QuickMick/zeta2/pcb/smd/zeta2/zeta2rework_lw_v6.brd

## EAGLE design pcb/smd/zeta2/zeta2rework_lw_v6.brd (2019-02-10, an earlier design)

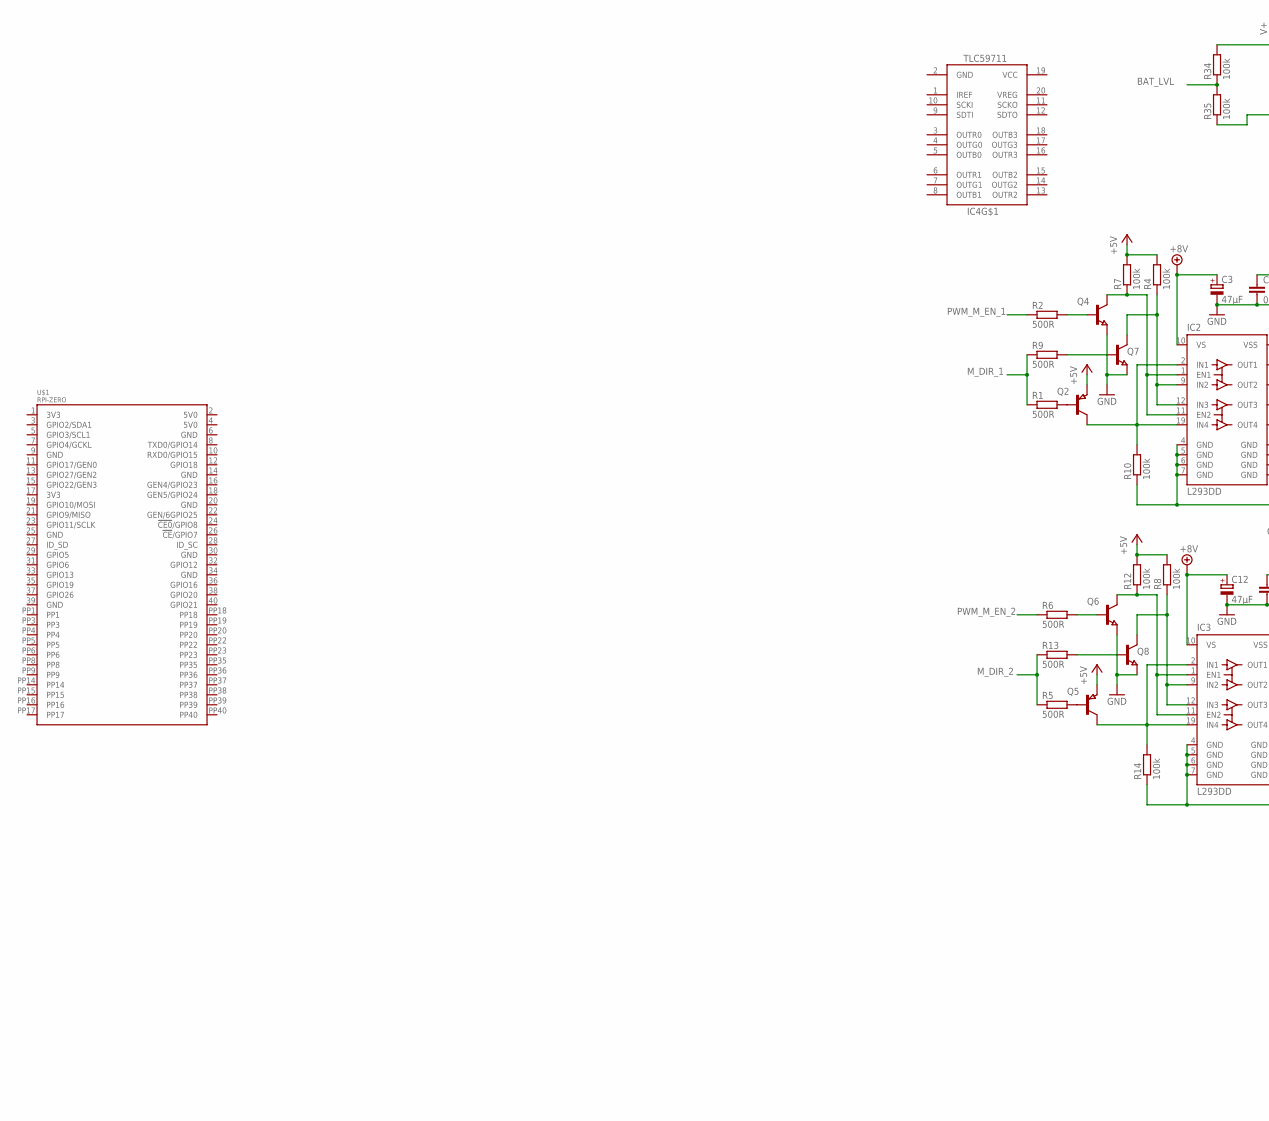
[picture p16: schematic zeta2rework_lw_v6.sch, part in row 1, column 1]

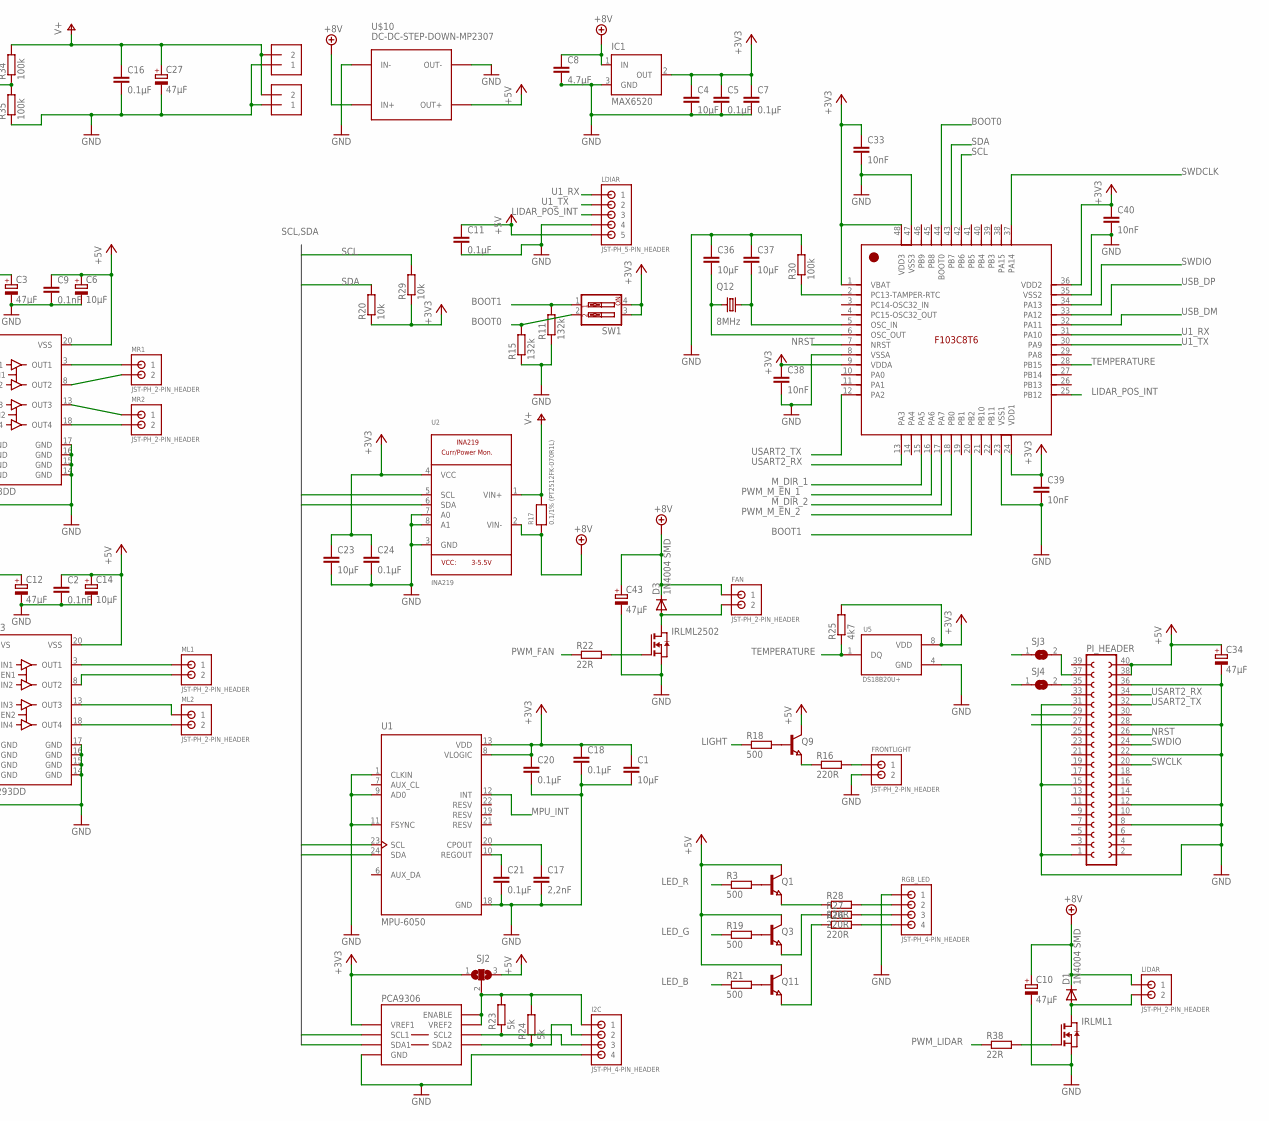
[picture p17: schematic zeta2rework_lw_v6.sch, part in row 1, column 2]

Parts:
C1, C4, C23, C36, C37: 10µF; C1206
C2, C9: 0.1nF; C1206
C3, C10, C12, C27, C34, C43: 47µF; UD-4X5,8_NICHICON
C5, C7, C11, C16, C18, C20, C21, C24: 0.1µF; C1206
C6, C14: 10µF; UD-4X5,8_NICHICON
C8: 4.7µF; C1206
C17: 2,2nF; C1206
C33, C38, C39, C40: 10nF; C1206
D1, D3: 1N4004 SMD; DO214AC
FAN: JST-PH_2-PIN_HEADER; JST_B2B-PH_HEADER
FRONTLIGHT: JST-PH_2-PIN_HEADER; JST_B2B-PH_HEADER
I2C: JST-PH_4-PIN_HEADER; JST_B4B-PH_HEADER
IC1: MAX6520; SOT23
IC2, IC3: L293DD; SO20
IC4: TLC59711; HTSSOP20DAP
IRLML1, IRLML2502: NMOSSOT23; SOT-23
LDIAR: JST-PH_5-PIN_HEADER; JST_B5B-PH_HEADER
LIDAR: JST-PH_2-PIN_HEADER; JST_B2B-PH_HEADER
ML1, ML2: JST-PH_2-PIN_HEADER; JST_B2B-PH_HEADER
MR1, MR2: JST-PH_2-PIN_HEADER; JST_B2B-PH_HEADER
PCA9306: IC2_LEVEL_TRANSLATER; SOIC-8
PI_HEADER: FE20-2
Q1, Q3, Q4, Q6, Q7, Q8, Q9, Q11: NPN-TRANSISTOR_SOT23; SOT23
Q2, Q5: PNP-TRANSISTOR_SOT23; SOT23
Q12: 8MHz; 7.0X5.0
R1, R2, R5, R6, R9, R13: 500R; R0603
R3, R19, R21: 500; R0603
R4, R7, R8, R10, R12, R14, R30, R34, R35: 100k; R0603
R11, R15: 132k; R0603
R16, R26, R27, R28: 220R; R0603
R17: 0.1/1% (PT2512FK-070R1L); 2512
R18: 500; R1206
R20, R29: 10k; R0603
R22, R38: 22R; R0603
R23, R24: 5k; R0603
R25: 4k7; R0603
RGB_LED: JST-PH_4-PIN_HEADER; JST_B4B-PH_HEADER
SJ2: SJ2W; SJ_2
SJ3, SJ4: SOLDERJUMPERREFLOW_NOPASTE; SOLDERJUMPER_REFLOW_NOPASTE
STM32F103CB: STM32F103CB; LQFP48_7X7MM_0.5MMPP
SUPPLY_IN, SUPPLY_IN1: TERMBLOCK_1X2-3.5MM; 1X2-3.5MM
SW1: SW_DIP-2; EDG-02
U1: MPU-6050; QFN50P400X400X95-24N
U2: INA219; SOT23-8
U5: DS18B20U+; SOP65P490X95-8N
U$1: RPI-ZERO; RASP_PI_ZERO_BOARD_FULL
U$10: DC-DC-STEP-DOWN-MP2307

Connections:
+3V3: C1.1, C4.1, C5.1, C7.1, C18.1, C20.1, C23.1, C24.1, C33.1, C38.1, C39.1, C40.1, IC1.2 (OUT), PCA9306.1 (VREF1), R20.1, R25.2, R29.1, SJ2.1, STM32F103CB.1 (VBAT), STM32F103CB.9 (VDDA), STM32F103CB.24 (VDD1), STM32F103CB.36 (VDD2), STM32F103CB.48 (VDD3), SW1.3, SW1.4, U1.8 (VLOGIC), U1.13 (VDD), U2.4 (VCC), U5.8 (VDD)
+5V: C2.1, C6.+, C9.1, C11.1, C14.+, C34.+, IC2.20 (VSS), IC3.20 (VSS), LDIAR.P5 (5), PI_HEADER.38, PI_HEADER.40, Q1.3 (C), Q2.2 (E), Q3.3 (C), Q5.2 (E), Q9.3 (C), Q11.3 (C), R4.2, R7.2, R8.2, R12.2, SJ2.3, U$10.OUT+
+8V: C3.+, C8.1, C10.+, C12.+, C43.+, D1.C, D3.C, FAN.P1 (1), IC1.1 (IN), IC2.10 (VS), IC3.10 (VS), LIDAR.P1 (1), R17.1, U2.2 (VIN-), U$10.IN+
BAT_LVL: R34.1, R35.2
BOOT0: R15.2, STM32F103CB.44 (BOOT0), SW1.2
BOOT1: R11.2, STM32F103CB.20 (PB2), SW1.1
BOOT2: PI_HEADER.29
BOOT3: PI_HEADER.27
GND: C1.2, C2.2, C3.-, C4.2, C5.2, C6.-, C7.2, C8.2, C9.2, C10.-, C11.2, C12.-, C14.-, C16.2, C17.2, C18.2, C20.2, C21.2, C23.2, C24.2, C27.-, C33.2, C34.-, C36.1, C37.1, C38.2, C39.2, C40.2, C43.-, FRONTLIGHT.P2 (2), I2C.P4 (4), IC1.3 (GND), IC2.4 (GND), IC2.5 (GND), IC2.6 (GND), IC2.7 (GND), IC2.14 (GND), IC2.15 (GND), IC2.16 (GND), IC2.17 (GND), IC3.4 (GND), IC3.5 (GND), IC3.6 (GND), IC3.7 (GND), IC3.14 (GND), IC3.15 (GND), IC3.16 (GND), IC3.17 (GND), IC4.2 (GND), IRLML1.2 (S), IRLML2502.2 (S), LDIAR.P4 (4), PCA9306.4 (GND), PI_HEADER.1, PI_HEADER.8, PI_HEADER.12, PI_HEADER.15, PI_HEADER.22, PI_HEADER.28, PI_HEADER.31, PI_HEADER.36, Q4.2 (E), Q6.2 (E), Q7.2 (E), Q8.2 (E), R10.1, R11.1, R14.1, R15.1, R30.2, R35.1, RGB_LED.P1 (1), STM32F103CB.8 (VSSA), STM32F103CB.23 (VSS1), STM32F103CB.35 (VSS2), STM32F103CB.47 (VSS3), SUPPLY_IN.1, SUPPLY_IN1.1, U1.1 (CLKIN), U1.9 (AD0), U1.11 (FSYNC), U1.18 (GND), U2.3 (GND), U2.7 (A0), U2.8 (A1), U5.4 (GND), U$10.IN-, U$10.OUT-
LED_B: R21.1
LED_G: R19.1
LED_R: R3.1
LIDAR_POS_INT: LDIAR.P3 (3), STM32F103CB.25 (PB12)
LIGHT: R18.1
MPU_INT: U1.12 (INT)
M_DIR_1: R1.1, R9.1, STM32F103CB.15 (PA5)
M_DIR_2: R5.1, R13.1, STM32F103CB.17 (PA7)
unnamed: IC2.9 (IN2), IC2.12 (IN3), Q7.3 (C), R4.1
unnamed: IC3.18 (OUT4), ML2.P2 (2)
unnamed: IC3.13 (OUT3), ML2.P1 (1)
unnamed: IC2.18 (OUT4), MR2.P2 (2)
unnamed: IC2.2 (IN1), IC2.19 (IN4), Q2.3 (C), R10.2
unnamed: IC3.9 (IN2), IC3.12 (IN3), Q8.3 (C), R8.1
unnamed: IC3.2 (IN1), IC3.19 (IN4), Q5.3 (C), R14.2
unnamed: IC2.1 (EN1), IC2.11 (EN2), Q4.3 (C), R7.1
unnamed: IC3.1 (EN1), IC3.11 (EN2), Q6.3 (C), R12.1
unnamed: Q2.1 (B), R1.2
unnamed: Q4.1 (B), R2.2
unnamed: Q7.1 (B), R9.2
unnamed: Q5.1 (B), R5.2
unnamed: Q6.1 (B), R6.2
unnamed: Q8.1 (B), R13.2
unnamed: IC2.13 (OUT3), MR2.P1 (1)
unnamed: IC2.8 (OUT2), MR1.P2 (2)
unnamed: IC2.3 (OUT1), MR1.P1 (1)
unnamed: Q9.1 (B), R18.2
unnamed: Q9.2 (E), R16.1
unnamed: FRONTLIGHT.P1 (1), R16.2
unnamed: Q1.1 (B), R3.2
unnamed: Q3.1 (B), R19.2
unnamed: Q1.2 (E), R28.1
unnamed: IC3.8 (OUT2), ML1.P2 (2)
unnamed: IC3.3 (OUT1), ML1.P1 (1)
unnamed: Q3.2 (E), R27.1
unnamed: Q11.2 (E), R26.1
unnamed: R26.2, RGB_LED.P4 (4)
unnamed: Q11.1 (B), R21.2
unnamed: R27.2, RGB_LED.P3 (3)
unnamed: C17.1, U1.20 (CPOUT)
unnamed: R28.2, RGB_LED.P2 (2)
unnamed: C21.1, U1.10 (REGOUT)
unnamed: IRLML2502.3 (G), R22.2
unnamed: IRLML1.3 (G), R38.2
unnamed: D1.A, IRLML1.1 (D), LIDAR.P2 (2)
unnamed: I2C.P1 (1), PCA9306.7 (VREF2), PCA9306.8 (ENABLE), R23.2, R24.2, SJ2.2
unnamed: I2C.P3 (3), PCA9306.6 (SCL2), R23.1
unnamed: I2C.P2 (2), PCA9306.5 (SDA2), R24.1
unnamed: PI_HEADER.37, SJ3.2
unnamed: PI_HEADER.35, SJ4.2
unnamed: C36.2, Q12.1, STM32F103CB.6 (OSC_OUT)
unnamed: C37.2, Q12.3 (2), STM32F103CB.5 (OSC_IN)
unnamed: R30.1, STM32F103CB.2 (PC13-TAMPER-RTC)
unnamed: D3.A, FAN.P2 (2), IRLML2502.1 (D)
NRST: PI_HEADER.26, STM32F103CB.7 (NRST)
PWM_FAN: R22.1
PWM_LIDAR: R38.1
PWM_M_EN_1: R2.1, STM32F103CB.16 (PA6)
PWM_M_EN_2: R6.1, STM32F103CB.18 (PB0)
SCL: R29.2, STM32F103CB.42 (PB6), U1.23 (SCL), U2.5 (SCL)
SCL2: PCA9306.2 (SCL1)
SCL3: SJ4.1
SDA: R20.2, STM32F103CB.43 (PB7), U1.24 (SDA), U2.6 (SDA)
SDA2: PCA9306.3 (SDA1)
SDA3: SJ3.1
SWCLK: PI_HEADER.20
SWDCLK: STM32F103CB.37 (PA14)
SWDIO: PI_HEADER.24, STM32F103CB.34 (PA13)
TEMPERATURE: R25.1, STM32F103CB.28 (PB15), U5.1 (DQ)
U1_RX: LDIAR.P1 (1), STM32F103CB.31 (PA10)
U1_TX: LDIAR.P2 (2), STM32F103CB.30 (PA9)
USART2_RX: PI_HEADER.34, STM32F103CB.13 (PA3)
USART2_TX: PI_HEADER.32, STM32F103CB.12 (PA2)
USB_DM: STM32F103CB.32 (PA11)
USB_DP: STM32F103CB.33 (PA12)
V+: C16.1, C27.+, R17.2, R34.2, SUPPLY_IN.2, SUPPLY_IN1.2, U2.1 (VIN+)
VCC: IC4.19 (VCC)

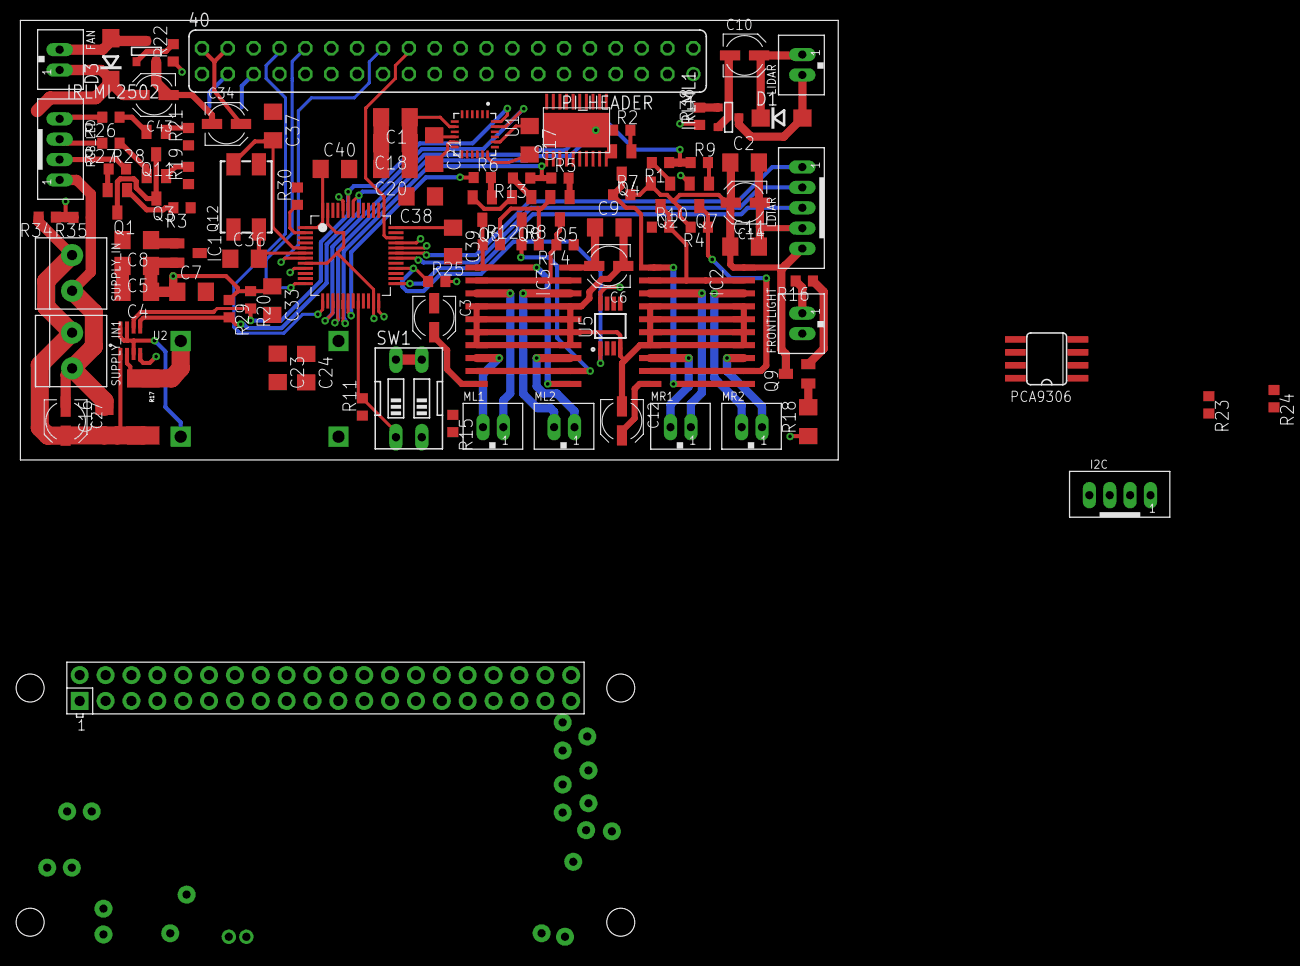
[picture p18: board zeta2rework_lw_v6.brd from above]

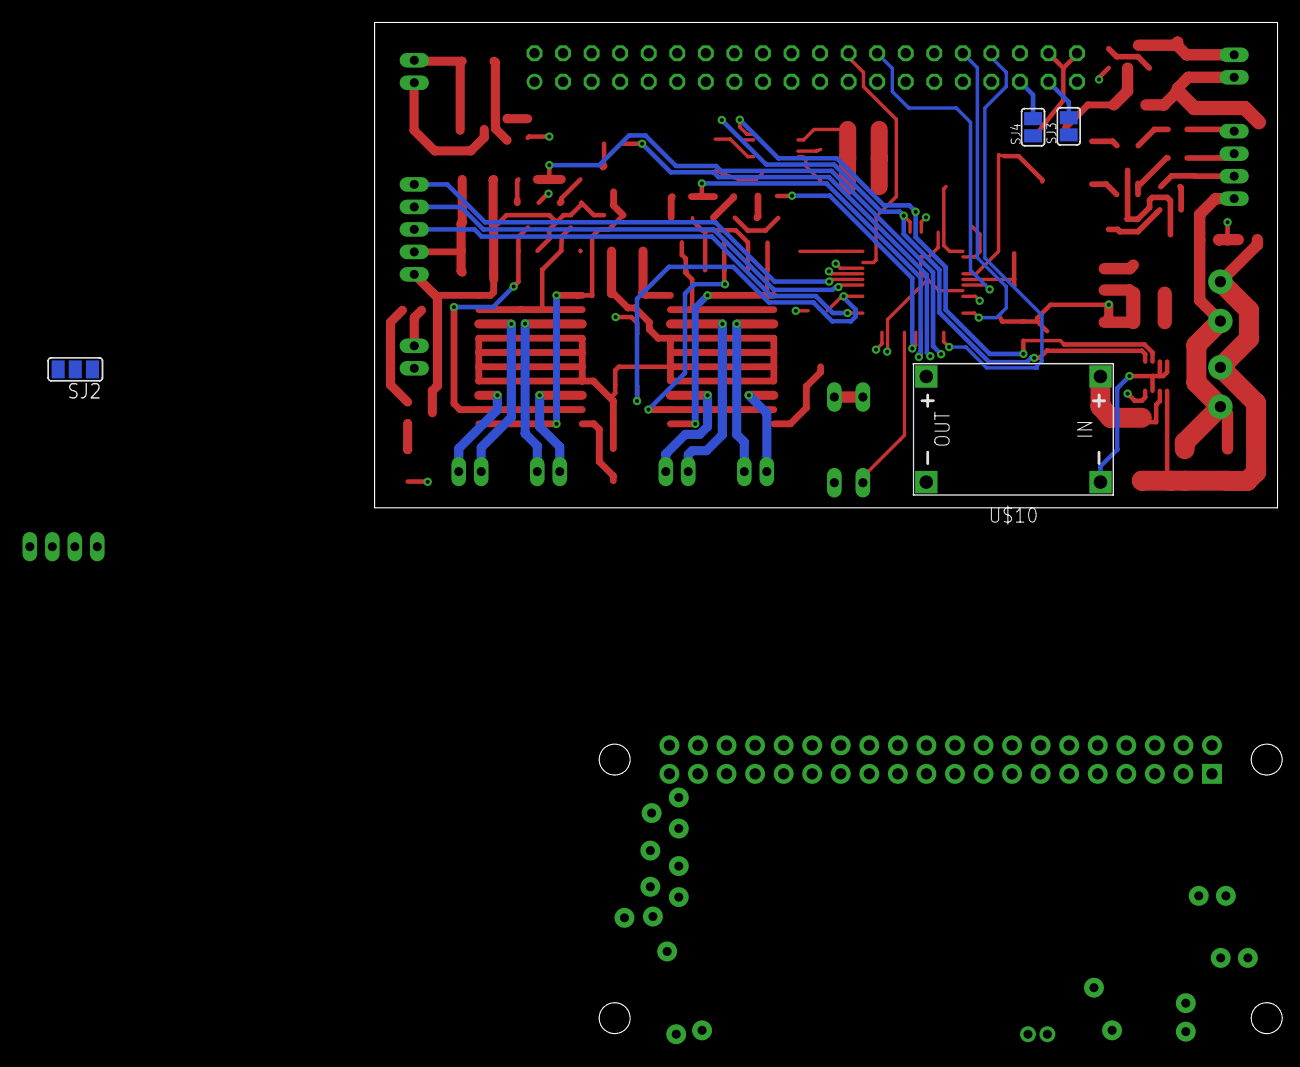
[picture p19: board zeta2rework_lw_v6.brd from below]

Board: 2 copper layers, 80.3 x 43.2 mm, 105 parts (4 on the bottom side), 68 nets.
