QuickMick/zeta2/pcb/smd/zeta2/zeta2rework_lw_v16.brd

## EAGLE design pcb/smd/zeta2/zeta2rework_lw_v16.brd (2019-02-10, an earlier design)

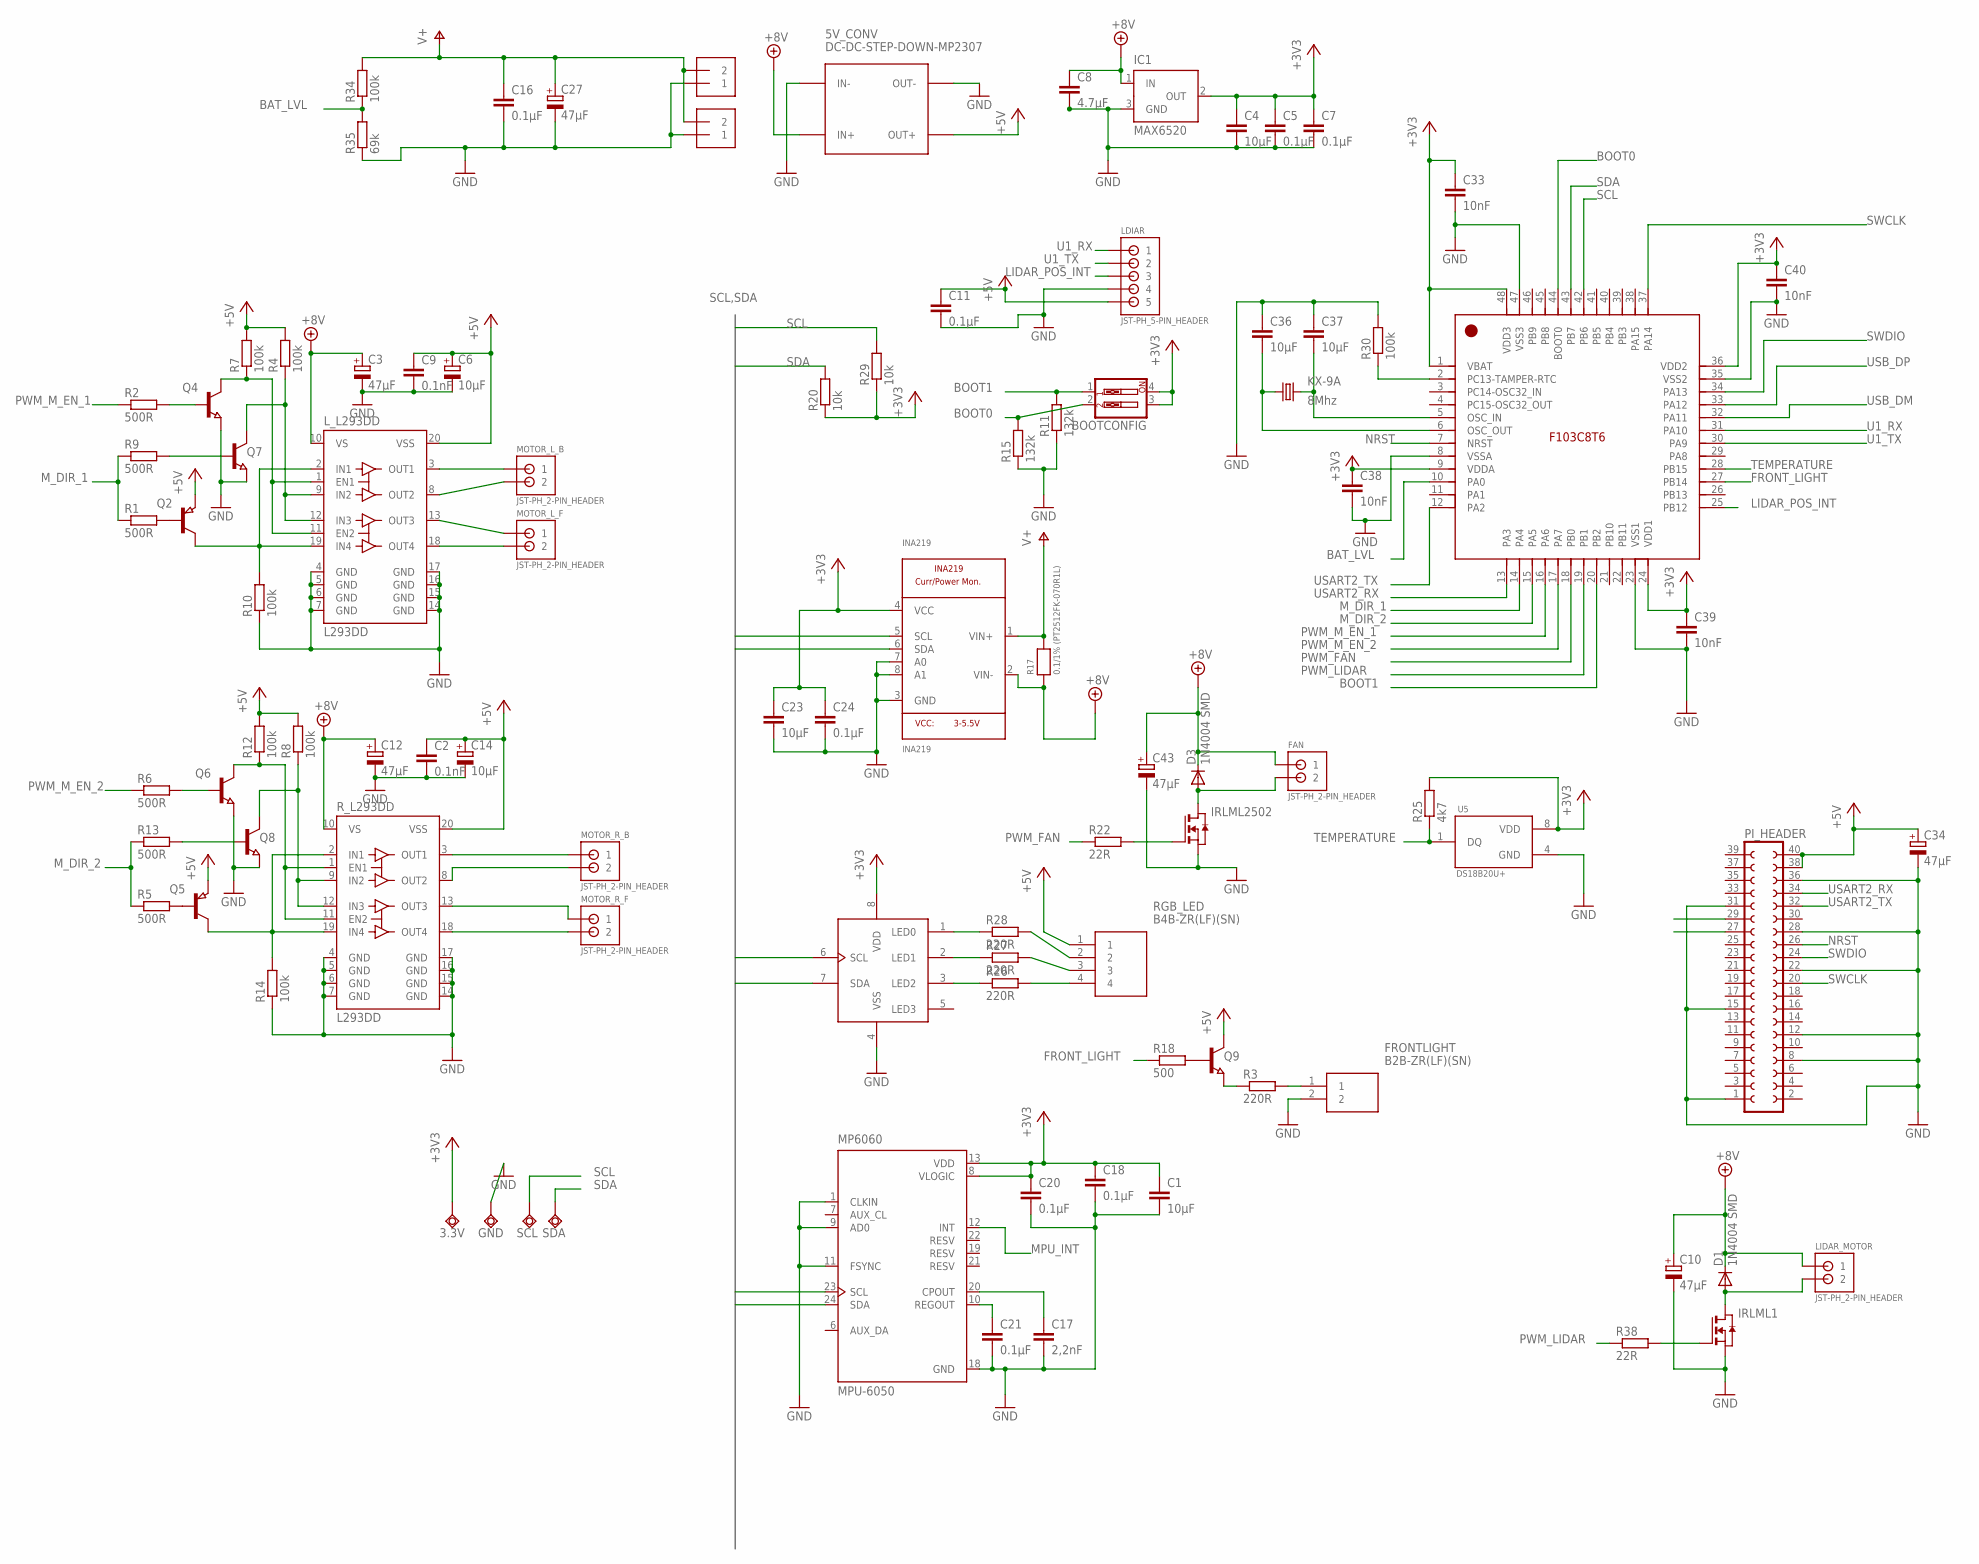
[picture p20: schematic zeta2rework_lw_v16.sch]

Parts:
3.3V: TPSQTP20R; TP20R
5V_CONV: DC-DC-STEP-DOWN-MP2307
BOOTCONFIG: SW_DIP-2; EDG-02
C1, C4, C23, C36, C37: 10µF; C1206
C2, C9: 0.1nF; C1206
C3, C10, C12, C27, C34, C43: 47µF; UD-4X5,8_NICHICON
C5, C7, C11, C16, C18, C20, C21, C24: 0.1µF; C1206
C6, C14: 10µF; UD-4X5,8_NICHICON
C8: 4.7µF; C1206
C17: 2,2nF; C1206
C33, C38, C39, C40: 10nF; C1206
D1, D3: 1N4004 SMD; DO214AC
FAN: JST-PH_2-PIN_HEADER; JST_B2B-PH_HEADER
FRONTLIGHT: B2B-ZR(LF)(SN); SHDR2W50P0X150_1X2_450X350X450
GND: TPSQTP20R; TP20R
IC1: MAX6520; SOT23
INA219: INA219; SOT23-8
IRLML1, IRLML2502: NMOSSOT23; SOT-23
KX-9A: 8Mhz; 5.0X3.2_KX-9A
LDIAR: JST-PH_5-PIN_HEADER; JST_B5B-PH_HEADER
LIDAR_MOTOR: JST-PH_2-PIN_HEADER; JST_B2B-PH_HEADER
L_L293DD: L293DD; SO20
MOTOR_L_B: JST-PH_2-PIN_HEADER; JST_B2B-PH_HEADER
MOTOR_L_F: JST-PH_2-PIN_HEADER; JST_B2B-PH_HEADER
MOTOR_R_B: JST-PH_2-PIN_HEADER; JST_B2B-PH_HEADER
MOTOR_R_F: JST-PH_2-PIN_HEADER; JST_B2B-PH_HEADER
MP6060: MPU-6050; QFN50P400X400X95-24N
PCA9533: PCA9533; SOIC8
PI_HEADER: FE20-2
Q2, Q5: PNP-TRANSISTOR_SOT23; SOT23
Q4, Q6, Q7, Q8, Q9: NPN-TRANSISTOR_SOT23; SOT23
R1, R2, R5, R6, R9, R13: 500R; R0603
R3, R26, R27, R28: 220R; R0603
R4, R7, R8, R10, R12, R14, R30, R34: 100k; R0603
R11, R15: 132k; R0603
R17: 0.1/1% (PT2512FK-070R1L); 2512
R18: 500; R1206
R20, R29: 10k; R0603
R22, R38: 22R; R0603
R25: 4k7; R0603
R35: 69k; R0603
RGB_LED: B4B-ZR(LF)(SN); SHDR4W50P0X150_1X4_750X350X450
R_L293DD: L293DD; SO20
SCL: TPSQTP20R; TP20R
SDA: TPSQTP20R; TP20R
STM32F103CB: STM32F103CB; LQFP48_7X7MM_0.5MMPP
SUPPLY_IN, SUPPLY_IN1: TERMBLOCK_1X2-3.5MM; 1X2-3.5MM
U5: DS18B20U+; SOP65P490X95-8N

Connections:
+3V3: 3.3V.TP, BOOTCONFIG.3, BOOTCONFIG.4, C1.1, C4.1, C5.1, C7.1, C18.1, C20.1, C23.1, C24.1, C33.1, C38.1, C39.1, C40.1, IC1.2 (OUT), INA219.4 (VCC), MP6060.8 (VLOGIC), MP6060.13 (VDD), PCA9533.8 (VDD), R20.1, R25.2, R29.1, STM32F103CB.1 (VBAT), STM32F103CB.9 (VDDA), STM32F103CB.24 (VDD1), STM32F103CB.36 (VDD2), STM32F103CB.48 (VDD3), U5.8 (VDD)
+5V: 5V_CONV.OUT+, C2.1, C6.+, C9.1, C11.1, C14.+, C34.+, LDIAR.P5 (5), L_L293DD.20 (VSS), PI_HEADER.38, PI_HEADER.40, Q2.2 (E), Q5.2 (E), Q9.3 (C), R4.2, R7.2, R8.2, R12.2, RGB_LED.1, R_L293DD.20 (VSS)
+8V: 5V_CONV.IN+, C3.+, C8.1, C10.+, C12.+, C43.+, D1.C, D3.C, FAN.P1 (1), IC1.1 (IN), INA219.2 (VIN-), LIDAR_MOTOR.P1 (1), L_L293DD.10 (VS), R17.1, R_L293DD.10 (VS)
BAT_LVL: R34.1, R35.2, STM32F103CB.10 (PA0)
BOOT0: BOOTCONFIG.2, R15.2, STM32F103CB.44 (BOOT0)
BOOT1: BOOTCONFIG.1, R11.2, STM32F103CB.20 (PB2)
BOOT2: PI_HEADER.29
BOOT3: PI_HEADER.27
FRONT_LIGHT: R18.1, STM32F103CB.27 (PB14)
GND: 5V_CONV.IN-, 5V_CONV.OUT-, C1.2, C2.2, C3.-, C4.2, C5.2, C6.-, C7.2, C8.2, C9.2, C10.-, C11.2, C12.-, C14.-, C16.2, C17.2, C18.2, C20.2, C21.2, C23.2, C24.2, C27.-, C33.2, C34.-, C36.1, C37.1, C38.2, C39.2, C40.2, C43.-, FRONTLIGHT.2, GND.TP, IC1.3 (GND), INA219.3 (GND), INA219.7 (A0), INA219.8 (A1), IRLML1.2 (S), IRLML2502.2 (S), LDIAR.P4 (4), L_L293DD.4 (GND), L_L293DD.5 (GND), L_L293DD.6 (GND), L_L293DD.7 (GND), L_L293DD.14 (GND), L_L293DD.15 (GND), L_L293DD.16 (GND), L_L293DD.17 (GND), MP6060.1 (CLKIN), MP6060.9 (AD0), MP6060.11 (FSYNC), MP6060.18 (GND), PCA9533.4 (VSS), PI_HEADER.1, PI_HEADER.8, PI_HEADER.12, PI_HEADER.15, PI_HEADER.22, PI_HEADER.28, PI_HEADER.31, PI_HEADER.36, Q4.2 (E), Q6.2 (E), Q7.2 (E), Q8.2 (E), R10.1, R11.1, R14.1, R15.1, R30.2, R35.1, R_L293DD.4 (GND), R_L293DD.5 (GND), R_L293DD.6 (GND), R_L293DD.7 (GND), R_L293DD.14 (GND), R_L293DD.15 (GND), R_L293DD.16 (GND), R_L293DD.17 (GND), STM32F103CB.8 (VSSA), STM32F103CB.23 (VSS1), STM32F103CB.35 (VSS2), STM32F103CB.47 (VSS3), SUPPLY_IN.1, SUPPLY_IN1.1, U5.4 (GND)
LIDAR_POS_INT: LDIAR.P3 (3), STM32F103CB.25 (PB12)
MPU_INT: MP6060.12 (INT)
M_DIR_1: R1.1, R9.1, STM32F103CB.14 (PA4)
M_DIR_2: R5.1, R13.1, STM32F103CB.15 (PA5)
unnamed: L_L293DD.9 (IN2), L_L293DD.12 (IN3), Q7.3 (C), R4.1
unnamed: MOTOR_R_F.P2 (2), R_L293DD.18 (OUT4)
unnamed: MOTOR_R_F.P1 (1), R_L293DD.13 (OUT3)
unnamed: L_L293DD.18 (OUT4), MOTOR_L_F.P2 (2)
unnamed: L_L293DD.2 (IN1), L_L293DD.19 (IN4), Q2.3 (C), R10.2
unnamed: Q8.3 (C), R8.1, R_L293DD.9 (IN2), R_L293DD.12 (IN3)
unnamed: Q5.3 (C), R14.2, R_L293DD.2 (IN1), R_L293DD.19 (IN4)
unnamed: L_L293DD.1 (EN1), L_L293DD.11 (EN2), Q4.3 (C), R7.1
unnamed: Q6.3 (C), R12.1, R_L293DD.1 (EN1), R_L293DD.11 (EN2)
unnamed: Q2.1 (B), R1.2
unnamed: Q4.1 (B), R2.2
unnamed: Q7.1 (B), R9.2
unnamed: Q5.1 (B), R5.2
unnamed: Q6.1 (B), R6.2
unnamed: Q8.1 (B), R13.2
unnamed: L_L293DD.13 (OUT3), MOTOR_L_F.P1 (1)
unnamed: L_L293DD.8 (OUT2), MOTOR_L_B.P2 (2)
unnamed: L_L293DD.3 (OUT1), MOTOR_L_B.P1 (1)
unnamed: Q9.1 (B), R18.2
unnamed: PCA9533.3 (LED2), R26.1
unnamed: PCA9533.2 (LED1), R27.1
unnamed: PCA9533.1 (LED0), R28.1
unnamed: MOTOR_R_B.P2 (2), R_L293DD.8 (OUT2)
unnamed: MOTOR_R_B.P1 (1), R_L293DD.3 (OUT1)
unnamed: Q9.2 (E), R3.1
unnamed: FRONTLIGHT.1, R3.2
unnamed: R26.2, RGB_LED.4
unnamed: R27.2, RGB_LED.3
unnamed: C17.1, MP6060.20 (CPOUT)
unnamed: R28.2, RGB_LED.2
unnamed: C21.1, MP6060.10 (REGOUT)
unnamed: IRLML2502.3 (G), R22.2
unnamed: IRLML1.3 (G), R38.2
unnamed: D1.A, IRLML1.1 (D), LIDAR_MOTOR.P2 (2)
unnamed: C36.2, KX-9A.1, STM32F103CB.6 (OSC_OUT)
unnamed: C37.2, KX-9A.3 (2), STM32F103CB.5 (OSC_IN)
unnamed: R30.1, STM32F103CB.2 (PC13-TAMPER-RTC)
unnamed: D3.A, FAN.P2 (2), IRLML2502.1 (D)
NRST: PI_HEADER.26, STM32F103CB.7 (NRST)
PWM_FAN: R22.1, STM32F103CB.18 (PB0)
PWM_LIDAR: R38.1, STM32F103CB.19 (PB1)
PWM_M_EN_1: R2.1, STM32F103CB.16 (PA6)
PWM_M_EN_2: R6.1, STM32F103CB.17 (PA7)
SCL: INA219.5 (SCL), MP6060.23 (SCL), PCA9533.6 (SCL), R29.2, SCL.TP, STM32F103CB.42 (PB6)
SDA: INA219.6 (SDA), MP6060.24 (SDA), PCA9533.7 (SDA), R20.2, SDA.TP, STM32F103CB.43 (PB7)
SWCLK: PI_HEADER.20, STM32F103CB.37 (PA14)
SWDIO: PI_HEADER.24, STM32F103CB.34 (PA13)
TEMPERATURE: R25.1, STM32F103CB.28 (PB15), U5.1 (DQ)
U1_RX: LDIAR.P1 (1), STM32F103CB.31 (PA10)
U1_TX: LDIAR.P2 (2), STM32F103CB.30 (PA9)
USART2_RX: PI_HEADER.34, STM32F103CB.13 (PA3)
USART2_TX: PI_HEADER.32, STM32F103CB.12 (PA2)
USB_DM: STM32F103CB.32 (PA11)
USB_DP: STM32F103CB.33 (PA12)
V+: C16.1, C27.+, INA219.1 (VIN+), R17.2, R34.2, SUPPLY_IN.2, SUPPLY_IN1.2

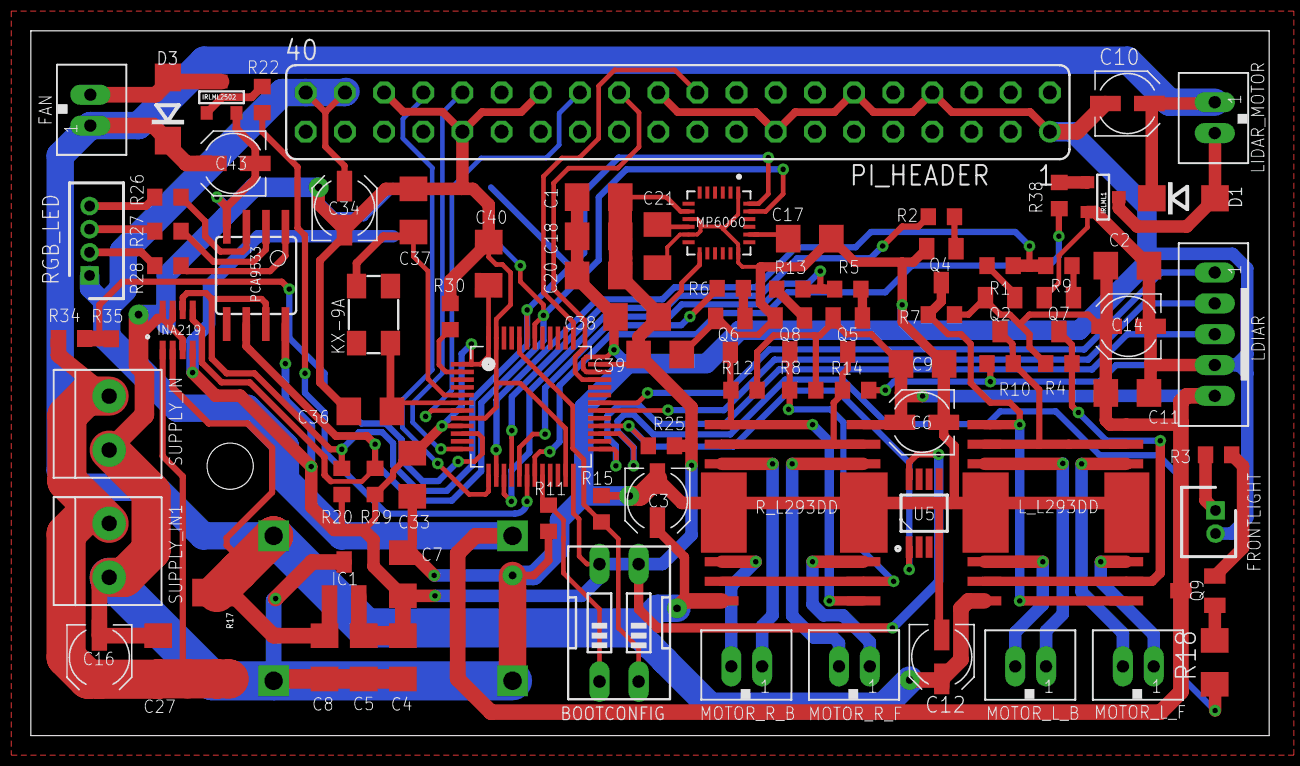
[picture p21: board zeta2rework_lw_v16.brd from above]

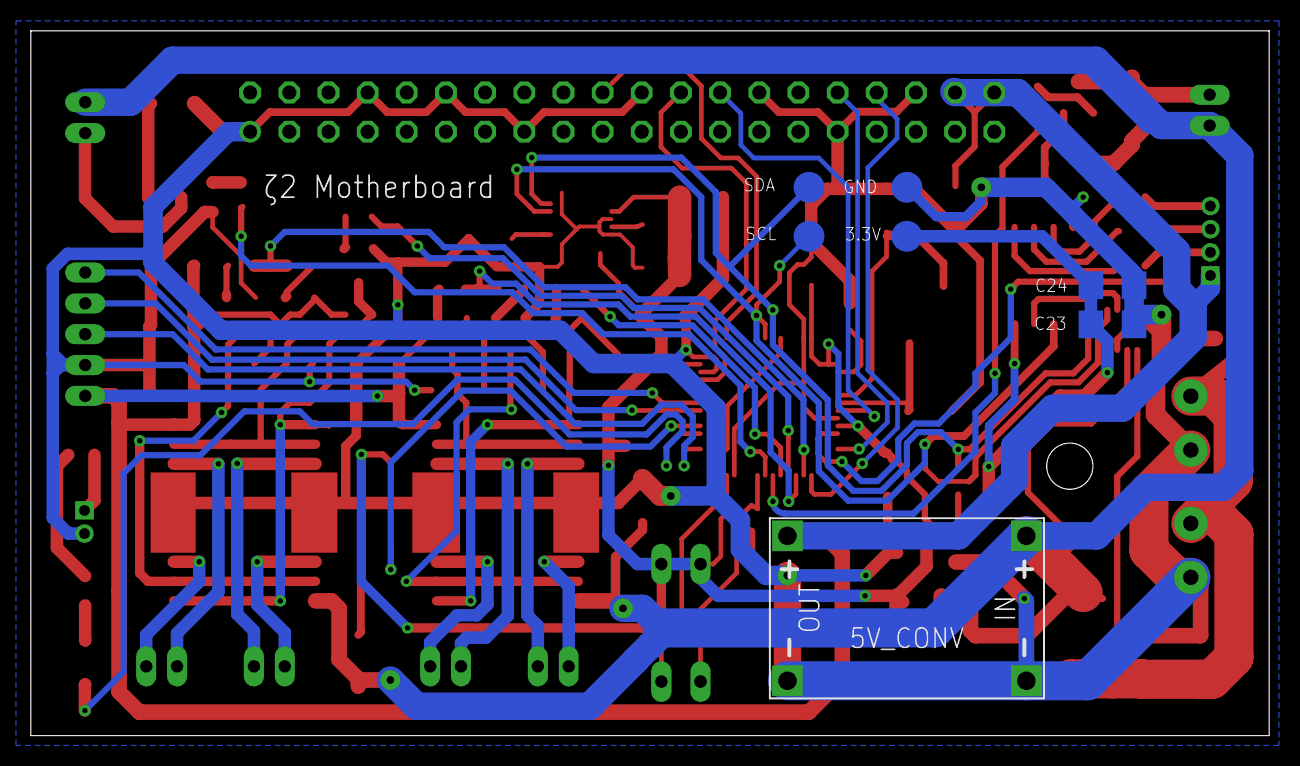
[picture p22: board zeta2rework_lw_v16.brd from below]

Board: 2 copper layers, 80.3 x 45.7 mm, 95 parts (7 on the bottom side), 64 nets.
