QuickMick/zeta2/pcb/smd/zeta2/zeta2rework.brd

## EAGLE design pcb/smd/zeta2/zeta2rework.brd (2019-02-05)

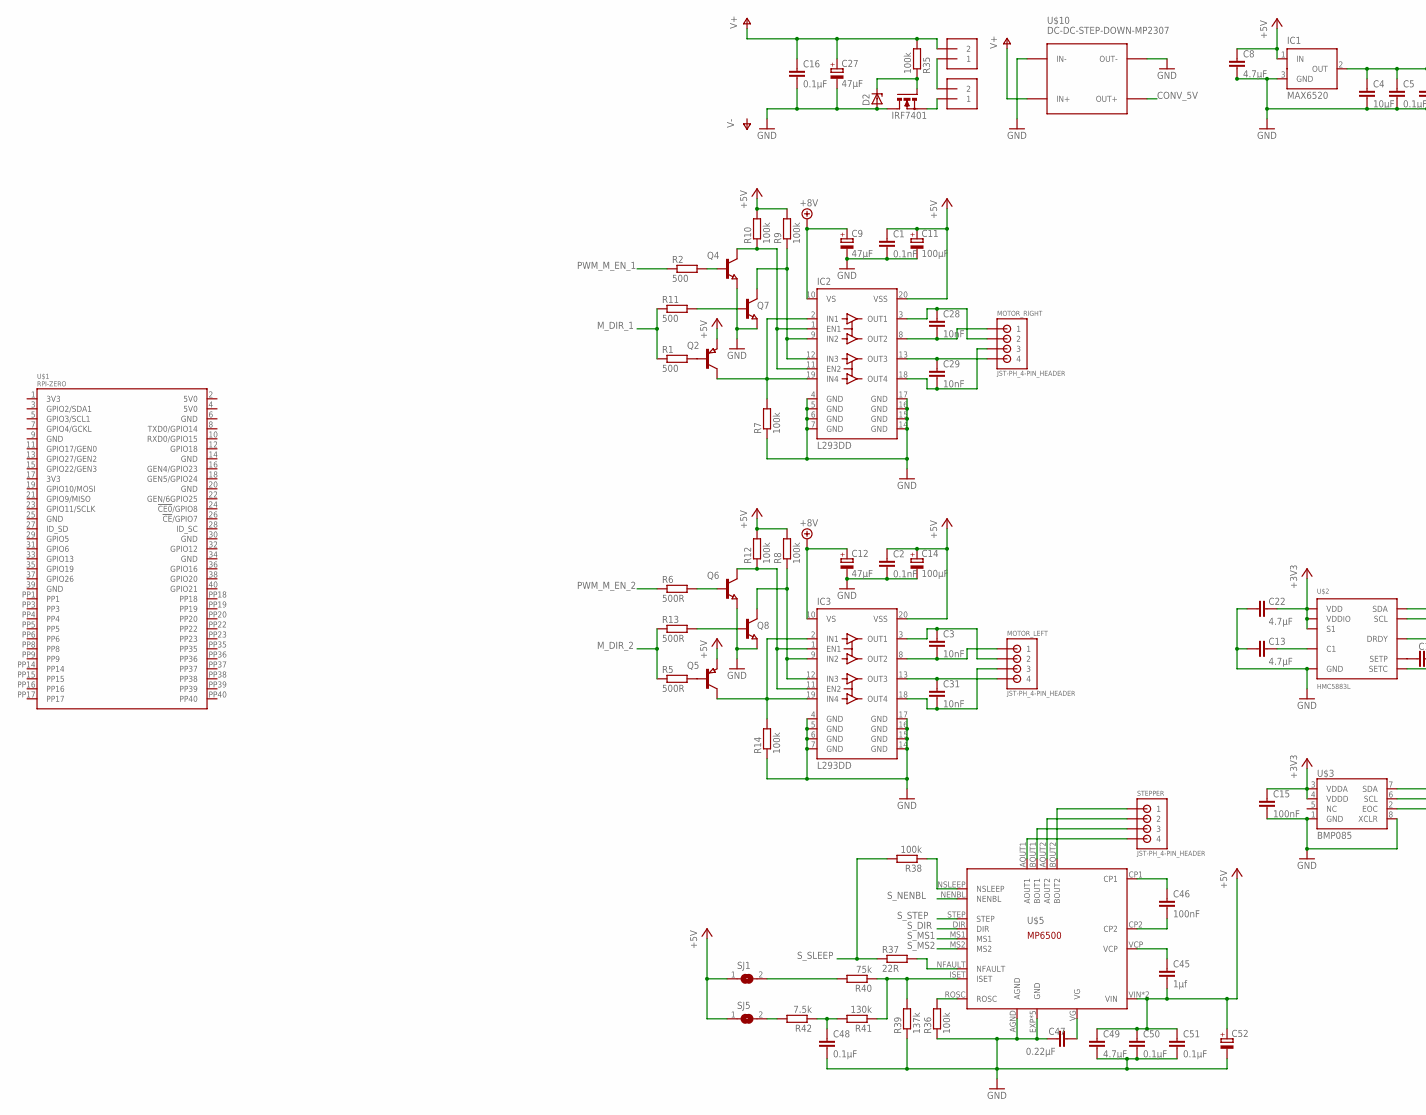
[picture p23: schematic zeta2rework.sch, part in row 1, column 1]

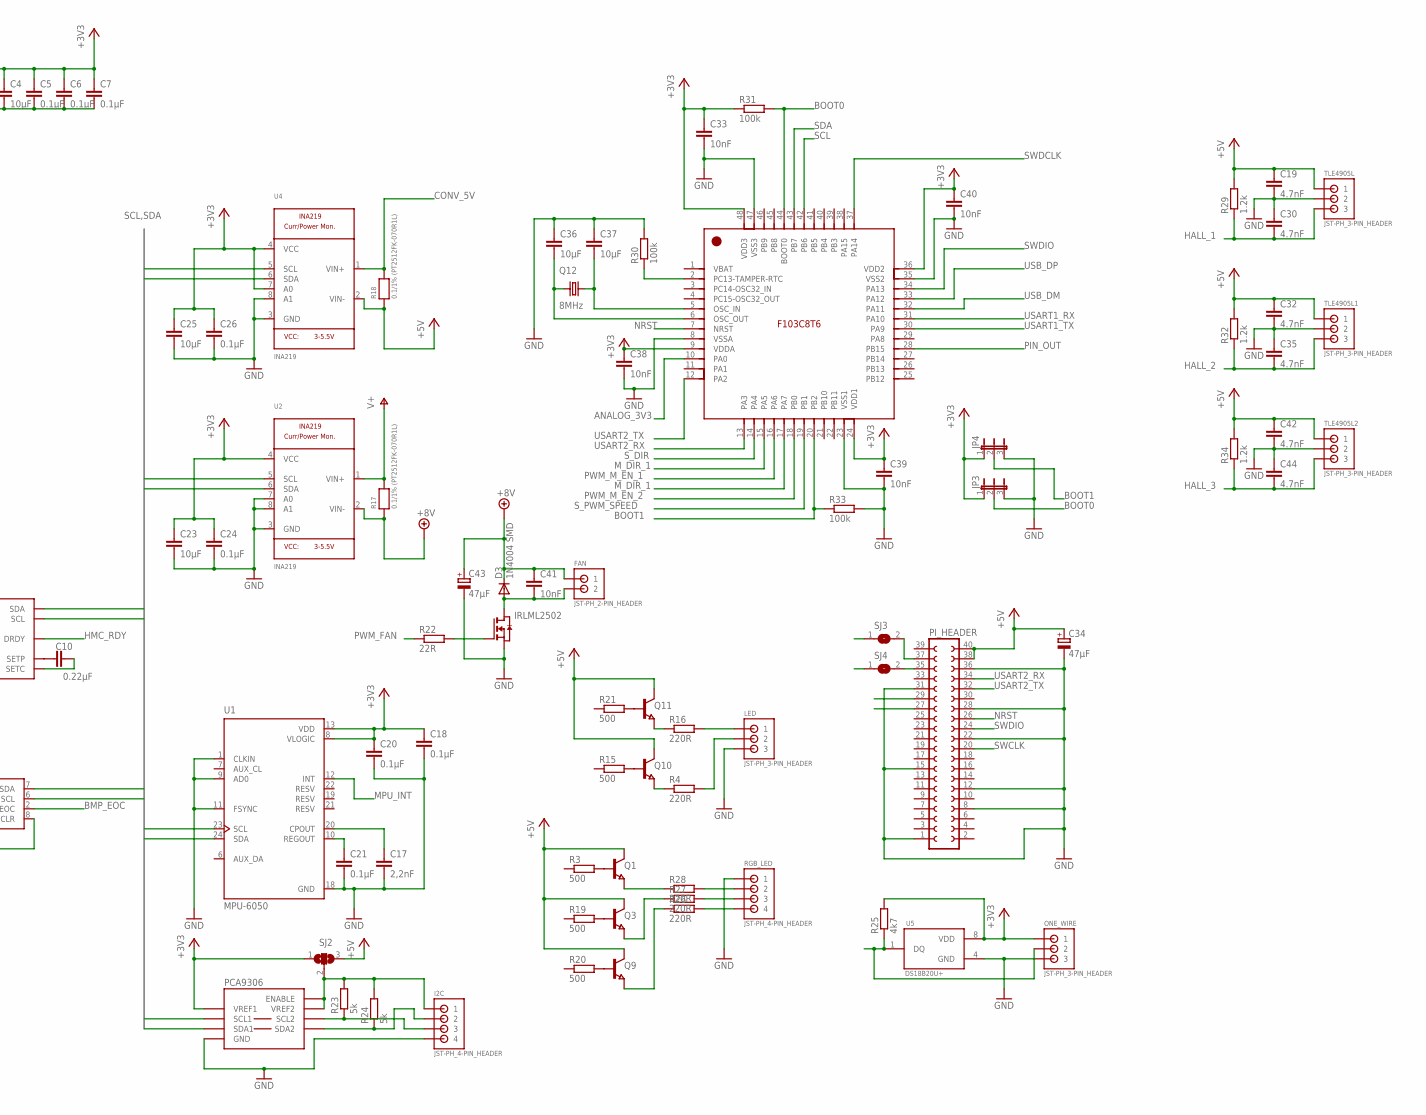
[picture p24: schematic zeta2rework.sch, part in row 1, column 2]

Parts:
C1, C2: 0.1nF; C0603
C3, C28, C29, C31, C33, C38, C39, C40, C41: 10nF; C0603
C4, C23, C25, C36, C37: 10µF; C0603
C5, C6, C7, C16, C18, C20, C21, C24, C26, C48, C50, C51: 0.1µF; C0603
C8, C13, C22, C49: 4.7µF; C0603
C9, C12, C27, C34, C43: 47µF; SMC_C
C10, C47: 0.22µF; C0603
C11, C14: 100µF; SMC_C
C15, C46: 100nF; C0603
C17: 2,2nF; C0603
C19, C30, C32, C35, C42, C44: 4.7nF; C0603
C45: 1µf; C0603
C52: CPOL-EU150CLZ-0810; 150CLZ-0810
D2: ZENER-DIODESOD80C; SOD80C
D3: 1N4004 SMD; MELF-MLL41
FAN: JST-PH_2-PIN_HEADER; JST_B2B-PH_HEADER
I2C: JST-PH_4-PIN_HEADER; JST_B4B-PH_HEADER
IC1: MAX6520; SOT23
IC2, IC3: L293DD; SO20
IRF7401: N-MOSFET-SO8S; SO-08
IRLML2502: NMOSSOT23; SOT-23
JP3, JP4: JP2E; JP2
LED: JST-PH_3-PIN_HEADER; JST_B3B-PH_HEADER
MOTOR_LEFT: JST-PH_4-PIN_HEADER; JST_B4B-PH_HEADER
MOTOR_RIGHT: JST-PH_4-PIN_HEADER; JST_B4B-PH_HEADER
ONE_WIRE: JST-PH_3-PIN_HEADER; JST_B3B-PH_HEADER
PCA9306: IC2_LEVEL_TRANSLATER; SOIC-8
PI_HEADER: FE20-2
Q1, Q3, Q4, Q6, Q7, Q8, Q9, Q10, Q11: NPN-TRANSISTOR_SOT23; SOT23
Q2, Q5: PNP-TRANSISTOR_SOT23; SOT23
Q12: 8MHz; 7.0X5.0
R1, R2, R3, R11, R15, R19, R20, R21: 500; R0603
R4, R16, R26, R27, R28: 220R; R0603
R5, R6, R13: 500R; R0603
R7, R8, R9, R10, R12, R14, R30, R31, R33, R35, R36, R38: 100k; R0603
R17, R18: 0.1/1% (PT2512FK-070R1L); 2512
R22, R37: 22R; R0603
R23, R24: 5k; R0603
R25: 4k7; R0603
R29, R32, R34: 1.2k; R0603
R39: 137k; R0603
R40: 75k; R0603
R41: 130k; R0603
R42: 7.5k; R0603
RGB_LED: JST-PH_4-PIN_HEADER; JST_B4B-PH_HEADER
SJ1, SJ3, SJ4, SJ5: SOLDERJUMPERREFLOW_NOPASTE; SOLDERJUMPER_REFLOW_NOPASTE
SJ2: SJ2W; SJ_2
STEPPER: JST-PH_4-PIN_HEADER; JST_B4B-PH_HEADER
SUPPLY_IN, SUPPLY_IN1: TERMBLOCK_1X2-3.5MM; 1X2-3.5MM
TLE4905L, TLE4905L1, TLE4905L2: JST-PH_3-PIN_HEADER; JST_B3B-PH_HEADER
U1: MPU-6050; QFN50P400X400X95-24N
U2, U4: INA219; SOT23-8
U5: DS18B20U+; SOP65P490X95-8N
U$1: RPI-ZERO; RASP_PI_ZERO_BOARD_FULL
U$2: HMC5883L; LPCC-16
U$3: BMP085
U$4: STM32F103C8T6; LQFP48_7X7MM_0.5MMPP
U$5: MP6500; QFN24
U$10: DC-DC-STEP-DOWN-MP2307

Connections:
+3V3: C4.1, C5.1, C6.1, C7.1, C15.1, C18.1, C20.1, C22.1, C23.1, C24.1, C25.1, C26.1, C33.1, C38.1, C39.1, C40.1, IC1.2 (OUT), JP3.1, JP4.1, ONE_WIRE.P1 (1), PCA9306.1 (VREF1), R25.2, R31.1, SJ2.1, U1.8 (VLOGIC), U1.13 (VDD), U2.4 (VCC), U4.4 (VCC), U4.7 (A0), U5.8 (VDD), U$2.2 (VDD), U$2.4 (S1), U$2.13 (VDDIO), U$3.3 (VDDA), U$3.4 (VDDD), U$4.9 (VDDA), U$4.24 (VDD1), U$4.36 (VDD2), U$4.48 (VDD3)
+5V: C1.1, C2.1, C8.1, C11.+, C14.+, C19.1, C32.1, C34.+, C42.1, C45.2, C49.1, C50.1, C51.1, C52.+, IC1.1 (IN), IC2.20 (VSS), IC3.20 (VSS), PI_HEADER.38, PI_HEADER.40, Q1.3 (C), Q2.2 (E), Q3.3 (C), Q5.2 (E), Q9.3 (C), Q10.3 (C), Q11.3 (C), R8.2, R9.2, R10.2, R12.2, R18.1, R29.2, R32.2, R34.2, SJ1.1, SJ2.3, SJ5.1, TLE4905L.P1 (1), TLE4905L1.P1 (1), TLE4905L2.P1 (1), U4.2 (VIN-), U$5.VIN, U$5.VIN@1 (VIN)
+8V: C9.+, C12.+, C41.1, C43.+, D3.C, FAN.P1 (1), IC2.10 (VS), IC3.10 (VS), R17.1, U2.2 (VIN-)
ANALOG_3V3: U$4.10 (PA0)
BMP_EOC: U$3.2 (EOC)
BOOT0: JP3.2, R31.2, U$4.44 (BOOT0)
BOOT1: JP4.2, R33.1, U$4.20 (PB2)
BOOT2: PI_HEADER.29
BOOT3: PI_HEADER.27
CONV_5V: R18.2, U4.1 (VIN+), U$10.OUT+
GND: C1.2, C2.2, C4.2, C5.2, C6.2, C7.2, C8.2, C9.-, C11.-, C12.-, C13.2, C14.-, C15.2, C16.2, C17.2, C18.2, C19.2, C20.2, C21.2, C22.2, C23.2, C24.2, C25.2, C26.2, C27.-, C30.1, C32.2, C33.2, C34.-, C35.1, C36.1, C37.1, C38.2, C39.2, C40.2, C42.2, C43.-, C44.1, C47.1, C48.2, C49.2, C50.2, C51.2, C52.-, D2.A, I2C.P4 (4), IC1.3 (GND), IC2.4 (GND), IC2.5 (GND), IC2.6 (GND), IC2.7 (GND), IC2.14 (GND), IC2.15 (GND), IC2.16 (GND), IC2.17 (GND), IC3.4 (GND), IC3.5 (GND), IC3.6 (GND), IC3.7 (GND), IC3.14 (GND), IC3.15 (GND), IC3.16 (GND), IC3.17 (GND), IRF7401.5 (D), IRF7401.6 (D), IRF7401.7 (D), IRF7401.8 (D), IRLML2502.2 (S), JP3.3, JP4.3, LED.P3 (3), ONE_WIRE.P3 (3), PCA9306.4 (GND), PI_HEADER.1, PI_HEADER.8, PI_HEADER.12, PI_HEADER.15, PI_HEADER.22, PI_HEADER.28, PI_HEADER.31, PI_HEADER.36, Q4.2 (E), Q6.2 (E), Q7.2 (E), Q8.2 (E), R7.1, R14.1, R30.2, R33.2, R36.1, R39.1, RGB_LED.P1 (1), TLE4905L.P2 (2), TLE4905L1.P2 (2), TLE4905L2.P2 (2), U1.1 (CLKIN), U1.9 (AD0), U1.11 (FSYNC), U1.18 (GND), U2.3 (GND), U2.7 (A0), U2.8 (A1), U4.3 (GND), U4.8 (A1), U5.4 (GND), U$2.9 (GND), U$2.11 (GND), U$3.1 (GND), U$3.8 (XCLR), U$4.8 (VSSA), U$4.23 (VSS1), U$4.35 (VSS2), U$4.47 (VSS3), U$5.AGND, U$5.EXP (GND), U$5.GND@1 (GND), U$5.GND@2 (GND), U$5.GND@3 (GND), U$5.GND@4 (GND), U$10.IN-, U$10.OUT-
HALL_1: C30.2, R29.1, TLE4905L.P3 (3)
HALL_2: C35.2, R32.1, TLE4905L1.P3 (3)
HALL_3: C44.2, R34.1, TLE4905L2.P3 (3)
HMC_RDY: U$2.15 (DRDY)
MPU_INT: U1.12 (INT)
M_DIR_1: R1.1, R11.1, U$4.15 (PA5), U$4.17 (PA7)
M_DIR_2: R5.1, R13.1
unnamed: IC2.9 (IN2), IC2.12 (IN3), Q7.3 (C), R9.1
unnamed: C31.2, IC3.18 (OUT4), MOTOR_LEFT.P3 (3)
unnamed: C31.1, IC3.13 (OUT3), MOTOR_LEFT.P4 (4)
unnamed: R26.2, RGB_LED.P4 (4)
unnamed: IC2.2 (IN1), IC2.19 (IN4), Q2.3 (C), R7.2
unnamed: IC3.9 (IN2), IC3.12 (IN3), Q8.3 (C), R8.1
unnamed: IC3.2 (IN1), IC3.19 (IN4), Q5.3 (C), R14.2
unnamed: IC2.1 (EN1), IC2.11 (EN2), Q4.3 (C), R10.1
unnamed: IC3.1 (EN1), IC3.11 (EN2), Q6.3 (C), R12.1
unnamed: Q2.1 (B), R1.2
unnamed: Q7.1 (B), R11.2
unnamed: Q4.1 (B), R2.2
unnamed: Q5.1 (B), R5.2
unnamed: Q6.1 (B), R6.2
unnamed: Q8.1 (B), R13.2
unnamed: R27.2, RGB_LED.P3 (3)
unnamed: C29.1, IC2.13 (OUT3), MOTOR_RIGHT.P4 (4)
unnamed: C29.2, IC2.18 (OUT4), MOTOR_RIGHT.P3 (3)
unnamed: R28.2, RGB_LED.P2 (2)
unnamed: C28.2, IC2.8 (OUT2), MOTOR_RIGHT.P1 (1)
unnamed: C28.1, IC2.3 (OUT1), MOTOR_RIGHT.P2 (2)
unnamed: Q1.1 (B), R3.2
unnamed: Q3.1 (B), R19.2
unnamed: Q1.2 (E), R28.1
unnamed: C3.2, IC3.8 (OUT2), MOTOR_LEFT.P1 (1)
unnamed: C3.1, IC3.3 (OUT1), MOTOR_LEFT.P2 (2)
unnamed: Q10.1 (B), R15.2
unnamed: Q3.2 (E), R27.1
unnamed: Q9.2 (E), R26.1
unnamed: Q10.2 (E), R4.1
unnamed: Q11.1 (B), R21.2
unnamed: Q9.1 (B), R20.2
unnamed: Q11.2 (E), R16.1
unnamed: C17.1, U1.20 (CPOUT)
unnamed: LED.P1 (1), R16.2
unnamed: C21.1, U1.10 (REGOUT)
unnamed: IRLML2502.3 (G), R22.2
unnamed: C10.2, U$2.12 (SETC)
unnamed: C10.1, U$2.8 (SETP)
unnamed: C13.1, U$2.10 (C1)
unnamed: I2C.P1 (1), PCA9306.7 (VREF2), PCA9306.8 (ENABLE), R23.2, R24.2, SJ2.2
unnamed: I2C.P3 (3), PCA9306.6 (SCL2), R23.1
unnamed: I2C.P2 (2), PCA9306.5 (SDA2), R24.1
unnamed: PI_HEADER.37, SJ3.2
unnamed: PI_HEADER.35, SJ4.2
unnamed: C36.2, Q12.1, U$4.6 (OSC_OUT)
unnamed: C37.2, Q12.3 (2), U$4.5 (OSC_IN)
unnamed: LED.P2 (2), R4.2
unnamed: R30.1, U$4.2 (PC13-TAMPER-RTC)
unnamed: SUPPLY_IN.1, SUPPLY_IN1.2
unnamed: C45.1, U$5.VCP
unnamed: R38.1, U$5.NSLEEP
unnamed: C46.2, U$5.CP2
unnamed: C46.1, U$5.CP1
unnamed: C41.2, D3.A, FAN.P2 (2), IRLML2502.1 (D)
unnamed: D2.C, IRF7401.4 (G), R35.1
unnamed: C47.2, U$5.VG
unnamed: R36.2, U$5.ROSC
unnamed: R37.2, U$5.NFAULT
unnamed: IRF7401.1 (S), IRF7401.2 (S), IRF7401.3 (S), SUPPLY_IN1.1
unnamed: STEPPER.P1 (1), U$5.BOUT2
unnamed: STEPPER.P2 (2), U$5.AOUT2
unnamed: R39.2, R40.1, R41.1, U$5.ISET
unnamed: STEPPER.P3 (3), U$5.BOUT1
unnamed: R40.2, SJ1.2
unnamed: R42.2, SJ5.2
unnamed: C48.1, R41.2, R42.1
unnamed: STEPPER.P4 (4), U$5.AOUT1
NRST: PI_HEADER.26, U$4.7 (NRST)
PIN_OUT: U$4.28 (PB15)
PWM_FAN: R22.1
PWM_M_EN_1: R2.1, U$4.16 (PA6)
PWM_M_EN_2: R6.1, U$4.18 (PB0)
SCL: U1.23 (SCL), U2.5 (SCL), U4.5 (SCL), U$3.6 (SCL), U$4.42 (PB6)
SCL1: U$2.1 (SCL)
SCL2: PCA9306.2 (SCL1)
SCL3: SJ4.1
SDA: U1.24 (SDA), U2.6 (SDA), U4.6 (SDA), U$3.7 (SDA), U$4.43 (PB7)
SDA1: U$2.16 (SDA)
SDA2: PCA9306.3 (SDA1)
SDA3: SJ3.1
SWCLK: PI_HEADER.20
SWDCLK: U$4.37 (PA14)
SWDIO: PI_HEADER.24, U$4.34 (PA13)
S_DIR: U$4.14 (PA4), U$5.DIR
S_MS1: U$5.MS1
S_MS2: U$5.MS2
S_NENBL: U$5.NENBL
S_PWM_SPEED: U$4.19 (PB1)
S_SLEEP: R37.1, R38.2
S_STEP: U$5.STEP
TEMPERATURE: ONE_WIRE.P2 (2), R25.1, U5.1 (DQ)
USART1_RX: U$4.31 (PA10)
USART1_TX: U$4.30 (PA9)
USART2_RX: PI_HEADER.34, U$4.13 (PA3)
USART2_TX: PI_HEADER.32, U$4.12 (PA2)
USB_DM: U$4.32 (PA11)
USB_DP: U$4.33 (PA12)
V+: C16.1, C27.+, R17.2, R35.2, SUPPLY_IN.2, U2.1 (VIN+), U$10.IN+

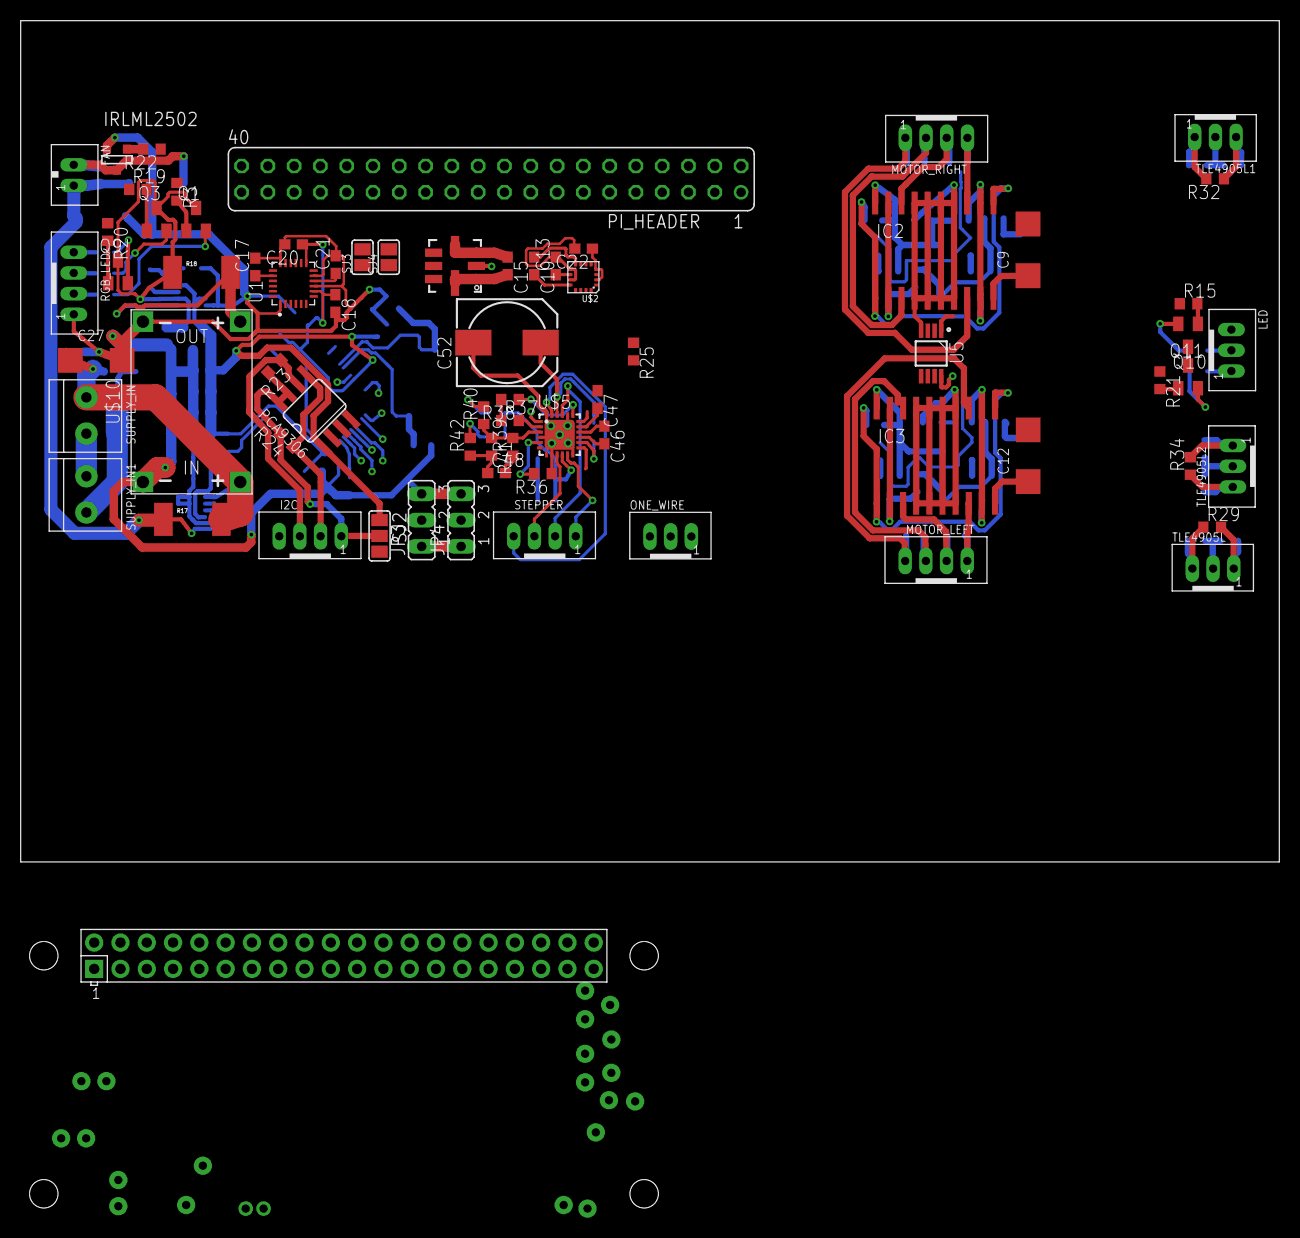
[picture p25: board zeta2rework.brd from above]

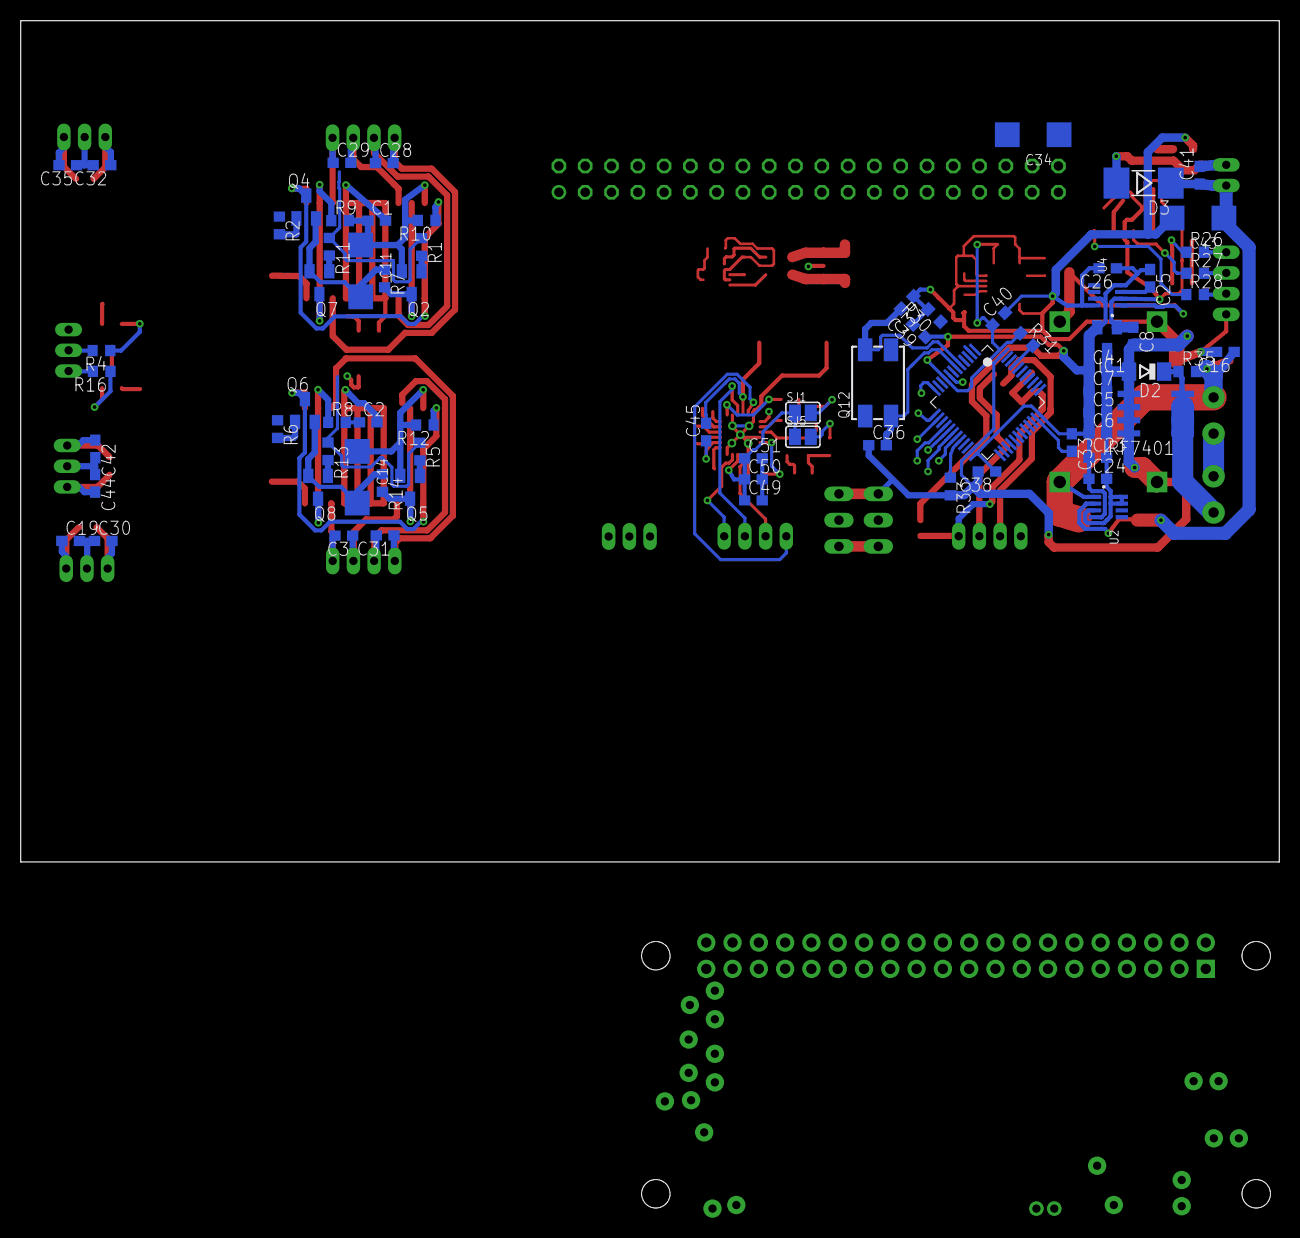
[picture p26: board zeta2rework.brd from below]

Board: 2 copper layers, 121.6 x 81.3 mm, 145 parts (74 on the bottom side), 92 nets.
