QuickMick/zeta2/pcb/smd/zeta2/zeta2_v2.brd

## EAGLE design pcb/smd/zeta2/zeta2_v2.brd (2018-07-10)

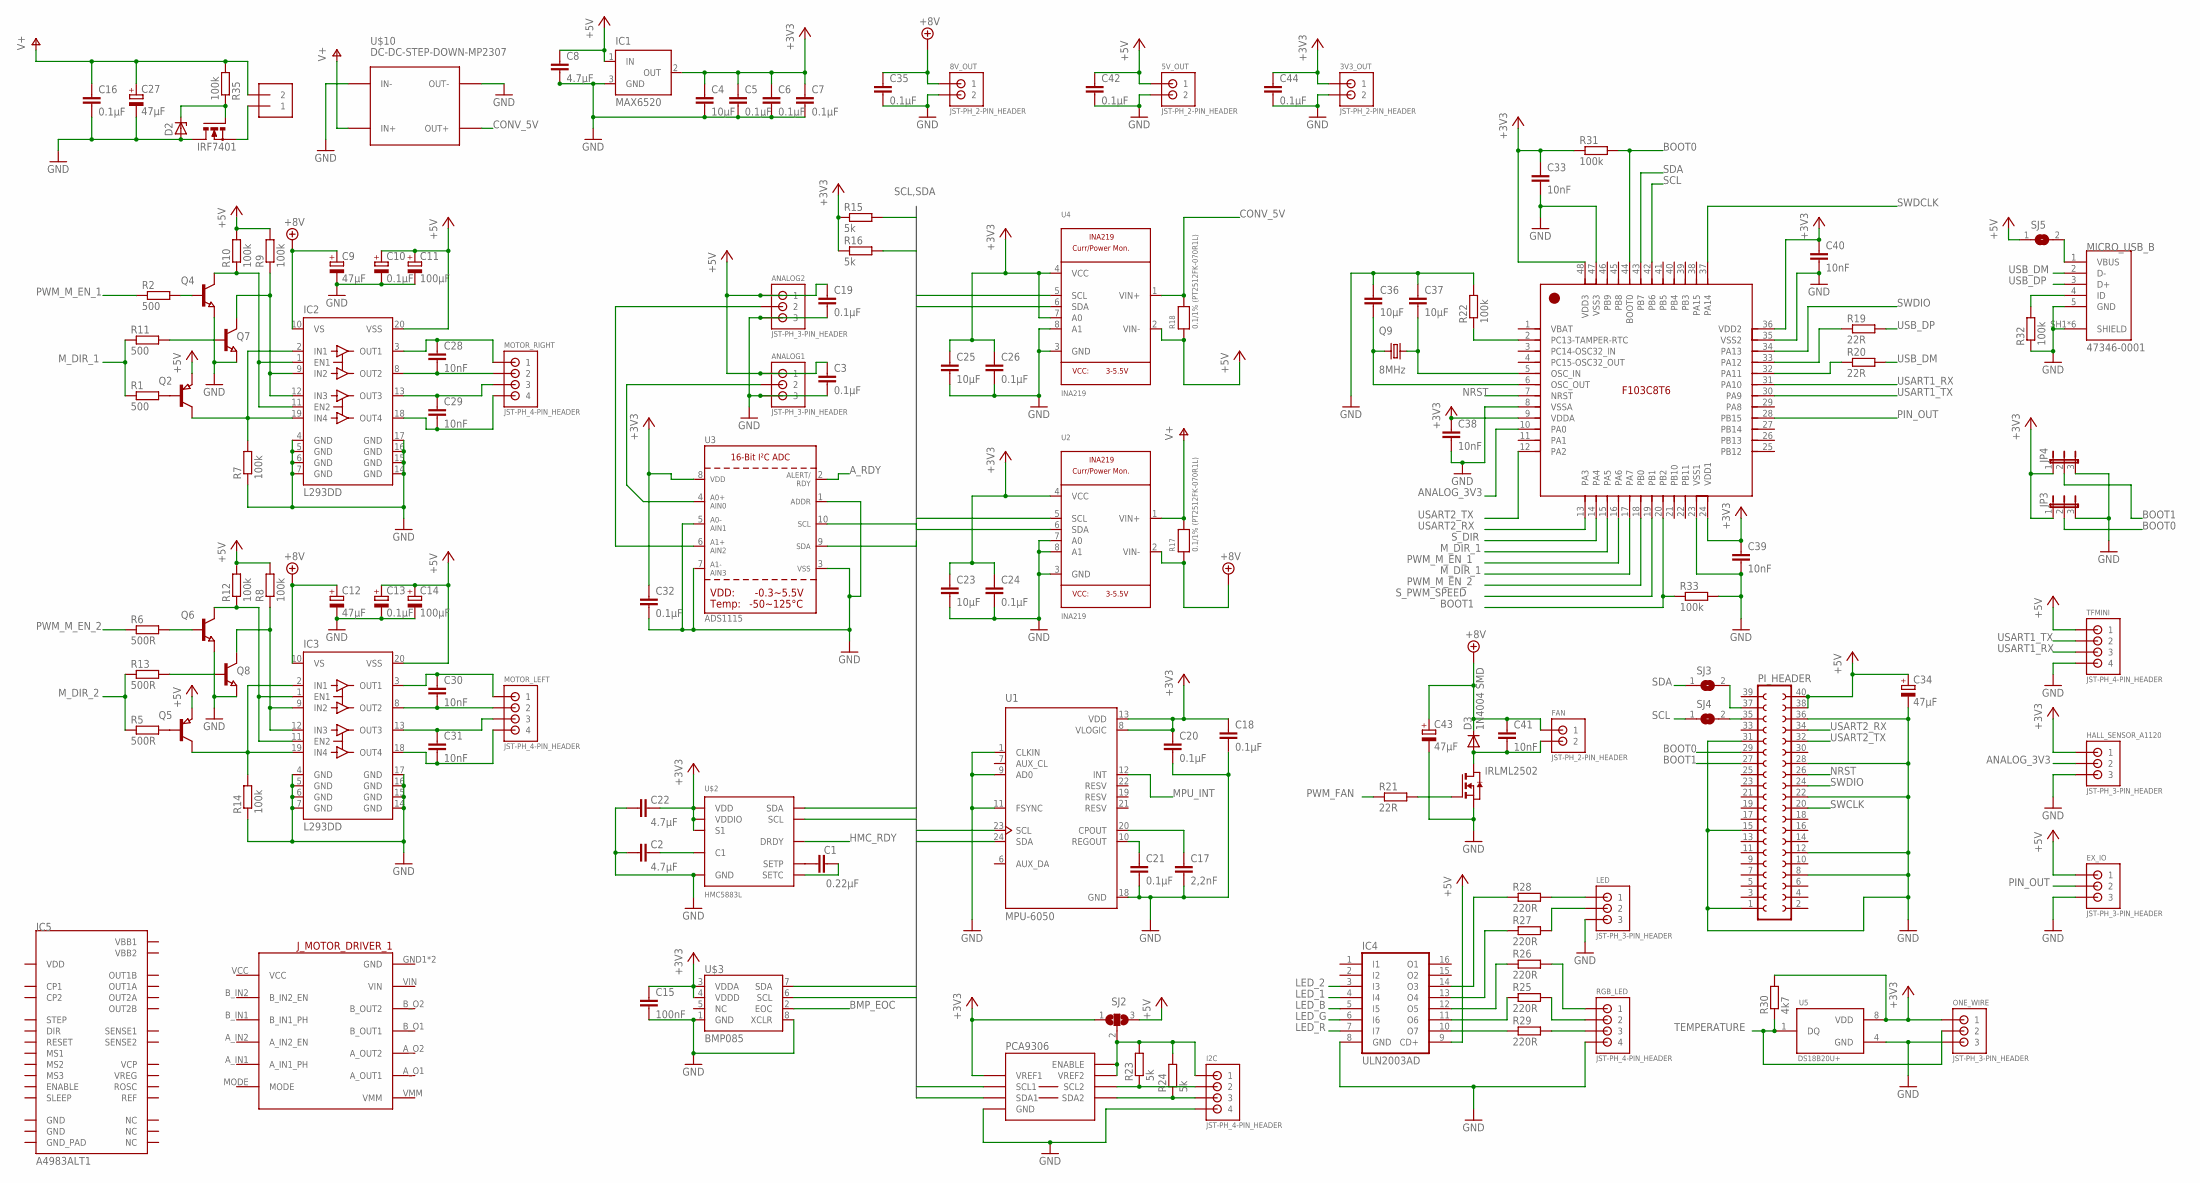
[picture p27: schematic zeta2_v2.sch]

Parts:
3V3_OUT, 5V_OUT, 8V_OUT: JST-PH_2-PIN_HEADER; JST_B2B-PH_HEADER
ANALOG1, ANALOG2: JST-PH_3-PIN_HEADER; JST_B3B-PH_HEADER
C1: 0.22µF; C0603
C2, C8, C22: 4.7µF; C0603
C3, C5, C6, C7, C16, C18, C19, C20, C21, C24, C26, C32, C35, C42, C44: 0.1µF; C0603
C4, C23, C25, C36, C37: 10µF; C0603
C9, C12, C27, C34, C43: 47µF; SMC_C
C10, C13: 0.1µF; SMC_A
C11, C14: 100µF; SMC_C
C15: 100nF; C0603
C17: 2,2nF; C0603
C28, C29, C30, C31, C33, C38, C39, C40, C41: 10nF; C0603
D2: ZENER-DIODESOD80C; SOD80C
D3: 1N4004 SMD; MELF-MLL41
EX_IO: JST-PH_3-PIN_HEADER; JST_B3B-PH_HEADER
FAN: JST-PH_2-PIN_HEADER; JST_B2B-PH_HEADER
HALL_SENSOR_A1120: JST-PH_3-PIN_HEADER; JST_B3B-PH_HEADER
I2C: JST-PH_4-PIN_HEADER; JST_B4B-PH_HEADER
IC1: MAX6520; SOT23
IC2, IC3: L293DD; SO20
IC4: ULN2003AD; SO16
IC5: A4983ALT1; QFN-28-5MM_ALT1
IRF7401: N-MOSFET-SO8S; SO-08
IRLML2502: NMOSSOT23; SOT-23
JP3, JP4: JP2E; JP2
J_MOTOR_DRIVER_1: MOTOR_DRIVER; MOTOR_DRIVER_FOOTPRINT
LED: JST-PH_3-PIN_HEADER; JST_B3B-PH_HEADER
MICRO_USB_B: 47346-0001; MOLEX_47346-0001
MOTOR_LEFT: JST-PH_4-PIN_HEADER; JST_B4B-PH_HEADER
MOTOR_RIGHT: JST-PH_4-PIN_HEADER; JST_B4B-PH_HEADER
ONE_WIRE: JST-PH_3-PIN_HEADER; JST_B3B-PH_HEADER
PCA9306: IC2_LEVEL_TRANSLATER; SOIC-8
PI_HEADER: FE20-2
Q2, Q5: PNP-TRANSISTOR_SOT23; SOT23
Q4, Q6, Q7, Q8: NPN-TRANSISTOR_SOT23; SOT23
Q9: 8MHz; 7.0X5.0
R1, R2, R11: 500; R0603
R5, R6, R13: 500R; R0603
R7, R8, R9, R10, R12, R14, R22, R31, R32, R33, R35: 100k; R0603
R15, R16, R23, R24: 5k; R0603
R17, R18: 0.1/1% (PT2512FK-070R1L); 2512
R19, R20, R21: 22R; R0603
R25, R26, R27, R28, R29: 220R; R0603
R30: 4k7; R0603
RGB_LED: JST-PH_4-PIN_HEADER; JST_B4B-PH_HEADER
SJ2: SJ2W; SJ_2
SJ3, SJ4, SJ5: SOLDERJUMPERREFLOW_NOPASTE; SOLDERJUMPER_REFLOW_NOPASTE
SUPPLY_IN: TERMBLOCK_1X2-3.5MM; 1X2-3.5MM
TFMINI: JST-PH_4-PIN_HEADER; JST_B4B-PH_HEADER
U1: MPU-6050; QFN50P400X400X95-24N
U2, U4: INA219; SOT23-8
U3: ADS1115; MSOP10
U5: DS18B20U+; SOP65P490X95-8N
U$1: STM32F103C8T6; LQFP48_7X7MM_0.5MMPP
U$2: HMC5883L; LPCC-16
U$3: BMP085
U$10: DC-DC-STEP-DOWN-MP2307

Connections:
+3V3: 3V3_OUT.P1 (1), C4.1, C5.1, C6.1, C7.1, C15.1, C18.1, C20.1, C22.1, C23.1, C24.1, C25.1, C26.1, C32.1, C33.1, C38.1, C39.1, C40.1, C44.1, HALL_SENSOR_A1120.P1 (1), IC1.2 (OUT), JP3.1, JP4.1, ONE_WIRE.P1 (1), PCA9306.1 (VREF1), R15.1, R16.1, R30.2, R31.1, SJ2.1, U1.8 (VLOGIC), U1.13 (VDD), U2.4 (VCC), U3.8 (VDD), U4.4 (VCC), U4.7 (A0), U5.8 (VDD), U$1.9 (VDDA), U$1.24 (VDD1), U$1.36 (VDD2), U$1.48 (VDD3), U$2.2 (VDD), U$2.4 (S1), U$2.13 (VDDIO), U$3.3 (VDDA), U$3.4 (VDDD)
+5V: 5V_OUT.P1 (1), ANALOG1.P1 (1), ANALOG2.P1 (1), C3.1, C8.1, C10.+, C11.+, C13.+, C14.+, C19.1, C34.+, C42.1, EX_IO.P1 (1), IC1.1 (IN), IC2.20 (VSS), IC3.20 (VSS), IC4.9 (CD+), PI_HEADER.38, PI_HEADER.40, Q2.2 (E), Q5.2 (E), R8.2, R9.2, R10.2, R12.2, R18.1, SJ2.3, SJ5.1, TFMINI.P1 (1), U4.2 (VIN-)
+8V: 8V_OUT.P1 (1), C9.+, C12.+, C35.1, C41.1, C43.+, D3.C, FAN.P1 (1), IC2.10 (VS), IC3.10 (VS), R17.1, U2.2 (VIN-)
ANALOG_3V3: HALL_SENSOR_A1120.P2 (2), U$1.10 (PA0)
A_RDY: U3.2 (ALERT/RDY)
BMP_EOC: U$3.2 (EOC)
BOOT0: JP3.2, PI_HEADER.29, R31.2, U$1.44 (BOOT0)
BOOT1: JP4.2, PI_HEADER.27, R33.1, U$1.20 (PB2)
CONV_5V: R18.2, U4.1 (VIN+), U$10.OUT+
GND: 3V3_OUT.P2 (2), 5V_OUT.P2 (2), 8V_OUT.P2 (2), ANALOG1.P3 (3), ANALOG2.P3 (3), C2.2, C3.2, C4.2, C5.2, C6.2, C7.2, C8.2, C9.-, C10.-, C11.-, C12.-, C13.-, C14.-, C15.2, C16.2, C17.2, C18.2, C19.2, C20.2, C21.2, C22.2, C23.2, C24.2, C25.2, C26.2, C27.-, C32.2, C33.2, C34.-, C35.2, C36.1, C37.1, C38.2, C39.2, C40.2, C42.2, C43.-, C44.2, D2.A, EX_IO.P3 (3), HALL_SENSOR_A1120.P3 (3), I2C.P4 (4), IC1.3 (GND), IC2.4 (GND), IC2.5 (GND), IC2.6 (GND), IC2.7 (GND), IC2.14 (GND), IC2.15 (GND), IC2.16 (GND), IC2.17 (GND), IC3.4 (GND), IC3.5 (GND), IC3.6 (GND), IC3.7 (GND), IC3.14 (GND), IC3.15 (GND), IC3.16 (GND), IC3.17 (GND), IC4.8 (GND), IC5.P$3 (GND), IC5.P$18 (GND), IRF7401.5 (D), IRF7401.6 (D), IRF7401.7 (D), IRF7401.8 (D), IRLML2502.2 (S), JP3.3, JP4.3, LED.P3 (3), MICRO_USB_B.5 (GND), MICRO_USB_B.SH1 (SHIELD), MICRO_USB_B.SH2 (SHIELD), MICRO_USB_B.SH3 (SHIELD), MICRO_USB_B.SH4 (SHIELD), MICRO_USB_B.SH5 (SHIELD), MICRO_USB_B.SH6 (SHIELD), ONE_WIRE.P3 (3), PCA9306.4 (GND), PI_HEADER.1, PI_HEADER.8, PI_HEADER.12, PI_HEADER.15, PI_HEADER.22, PI_HEADER.28, PI_HEADER.31, PI_HEADER.36, Q4.2 (E), Q6.2 (E), Q7.2 (E), Q8.2 (E), R7.1, R14.1, R22.2, R32.1, R33.2, RGB_LED.P4 (4), TFMINI.P4 (4), U1.1 (CLKIN), U1.9 (AD0), U1.11 (FSYNC), U1.18 (GND), U2.3 (GND), U2.7 (A0), U2.8 (A1), U3.1 (ADDR), U3.3 (VSS), U3.5 (AIN1), U3.7 (AIN3), U4.3 (GND), U4.8 (A1), U5.4 (GND), U$1.8 (VSSA), U$1.23 (VSS1), U$1.35 (VSS2), U$1.47 (VSS3), U$2.9 (GND), U$2.11 (GND), U$3.1 (GND), U$3.8 (XCLR), U$10.IN-, U$10.OUT-
GND_PAD: IC5.P$29 (GND_PAD)
HMC_RDY: U$2.15 (DRDY)
LED_1: IC4.4 (I4)
LED_2: IC4.3 (I3)
LED_B: IC4.5 (I5)
LED_G: IC4.6 (I6)
LED_R: IC4.7 (I7)
MPU_INT: U1.12 (INT)
M_DIR_1: R1.1, R11.1, U$1.15 (PA5), U$1.17 (PA7)
M_DIR_2: R5.1, R13.1
unnamed: IC2.9 (IN2), IC2.12 (IN3), Q7.3 (C), R9.1
unnamed: C1.2, U$2.12 (SETC)
unnamed: C1.1, U$2.8 (SETP)
unnamed: C2.1, U$2.10 (C1)
unnamed: IC2.2 (IN1), IC2.19 (IN4), Q2.3 (C), R7.2
unnamed: IC3.9 (IN2), IC3.12 (IN3), Q8.3 (C), R8.1
unnamed: IC3.2 (IN1), IC3.19 (IN4), Q5.3 (C), R14.2
unnamed: IC2.1 (EN1), IC2.11 (EN2), Q4.3 (C), R10.1
unnamed: IC3.1 (EN1), IC3.11 (EN2), Q6.3 (C), R12.1
unnamed: Q2.1 (B), R1.2
unnamed: Q7.1 (B), R11.2
unnamed: Q4.1 (B), R2.2
unnamed: Q5.1 (B), R5.2
unnamed: Q6.1 (B), R6.2
unnamed: Q8.1 (B), R13.2
unnamed: C17.1, U1.20 (CPOUT)
unnamed: C29.1, IC2.13 (OUT3), MOTOR_RIGHT.P3 (3)
unnamed: C29.2, IC2.18 (OUT4), MOTOR_RIGHT.P4 (4)
unnamed: C21.1, U1.10 (REGOUT)
unnamed: C28.2, IC2.8 (OUT2), MOTOR_RIGHT.P2 (2)
unnamed: C28.1, IC2.3 (OUT1), MOTOR_RIGHT.P1 (1)
unnamed: C31.1, IC3.13 (OUT3), MOTOR_LEFT.P3 (3)
unnamed: C31.2, IC3.18 (OUT4), MOTOR_LEFT.P4 (4)
unnamed: C30.2, IC3.8 (OUT2), MOTOR_LEFT.P2 (2)
unnamed: C30.1, IC3.3 (OUT1), MOTOR_LEFT.P1 (1)
unnamed: IC4.10 (O7), R29.1
unnamed: C36.2, Q9.1, U$1.6 (OSC_OUT)
unnamed: C37.2, Q9.3 (2), U$1.5 (OSC_IN)
unnamed: IRLML2502.3 (G), R21.2
unnamed: IC4.11 (O6), R25.1
unnamed: R20.1, U$1.32 (PA11)
unnamed: R19.1, U$1.33 (PA12)
unnamed: R22.1, U$1.2 (PC13-TAMPER-RTC)
unnamed: PI_HEADER.37, SJ3.2
unnamed: PI_HEADER.35, SJ4.2
unnamed: IC4.12 (O5), R26.1
unnamed: I2C.P1 (1), PCA9306.7 (VREF2), PCA9306.8 (ENABLE), R23.2, R24.2, SJ2.2
unnamed: I2C.P2 (2), PCA9306.6 (SCL2), R23.1
unnamed: I2C.P3 (3), PCA9306.5 (SDA2), R24.1
unnamed: IC4.13 (O4), R27.1
unnamed: IC4.14 (O3), R28.1
unnamed: MICRO_USB_B.4 (ID), R32.2
unnamed: LED.P1 (1), R28.2
unnamed: R29.2, RGB_LED.P3 (3)
unnamed: R25.2, RGB_LED.P2 (2)
unnamed: R26.2, RGB_LED.P1 (1)
unnamed: LED.P2 (2), R27.2
unnamed: MICRO_USB_B.1 (VBUS), SJ5.2
unnamed: ANALOG1.P2 (2), U3.4 (AIN0)
unnamed: ANALOG2.P2 (2), U3.6 (AIN2)
unnamed: C41.2, D3.A, FAN.P2 (2), IRLML2502.1 (D)
unnamed: D2.C, IRF7401.4 (G), R35.1
unnamed: IRF7401.1 (S), IRF7401.2 (S), IRF7401.3 (S), SUPPLY_IN.1
NRST: PI_HEADER.26, U$1.7 (NRST)
PIN_OUT: EX_IO.P2 (2), U$1.28 (PB15)
PWM_FAN: R21.1
PWM_M_EN_1: R2.1, U$1.16 (PA6)
PWM_M_EN_2: R6.1, U$1.18 (PB0)
SCL: PCA9306.2 (SCL1), R15.2, SJ4.1, U1.23 (SCL), U2.5 (SCL), U3.10 (SCL), U4.5 (SCL), U$1.42 (PB6), U$2.1 (SCL), U$3.6 (SCL)
SDA: PCA9306.3 (SDA1), R16.2, SJ3.1, U1.24 (SDA), U2.6 (SDA), U3.9 (SDA), U4.6 (SDA), U$1.43 (PB7), U$2.16 (SDA), U$3.7 (SDA)
SWCLK: PI_HEADER.20
SWDCLK: U$1.37 (PA14)
SWDIO: PI_HEADER.24, U$1.34 (PA13)
S_DIR: U$1.14 (PA4)
S_PWM_SPEED: U$1.19 (PB1)
TEMPERATURE: ONE_WIRE.P2 (2), R30.1, U5.1 (DQ)
USART1_RX: TFMINI.P3 (3), U$1.31 (PA10)
USART1_TX: TFMINI.P2 (2), U$1.30 (PA9)
USART2_RX: PI_HEADER.34, U$1.13 (PA3)
USART2_TX: PI_HEADER.32, U$1.12 (PA2)
USB_DM: MICRO_USB_B.2 (D-), R20.2
USB_DP: MICRO_USB_B.3 (D+), R19.2
V+: C16.1, C27.+, R17.2, R35.2, SUPPLY_IN.2, U2.1 (VIN+), U$10.IN+
VDD: IC5.P$15 (VDD)

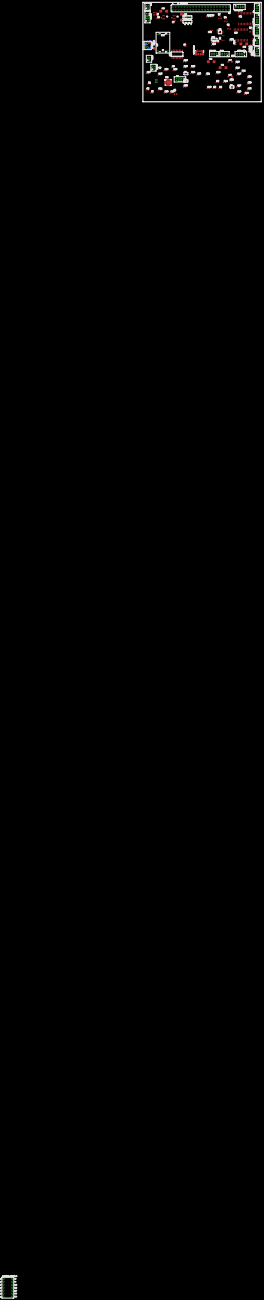
[picture p28: board zeta2_v2.brd from above]

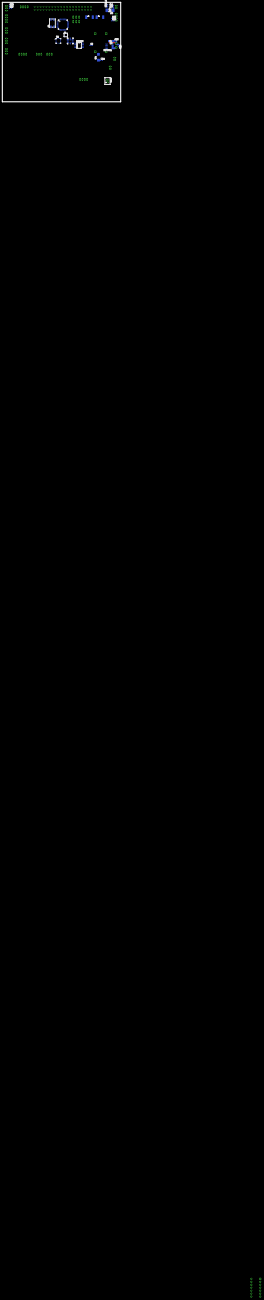
[picture p29: board zeta2_v2.brd from below]

Board: 2 copper layers, 101.3 x 85.1 mm, 127 parts (24 on the bottom side), 78 nets.
